sms1875/ModuCar/modeling/0217 프론트에 보여줄 이미지 추출/10. 냉동모듈.JPG

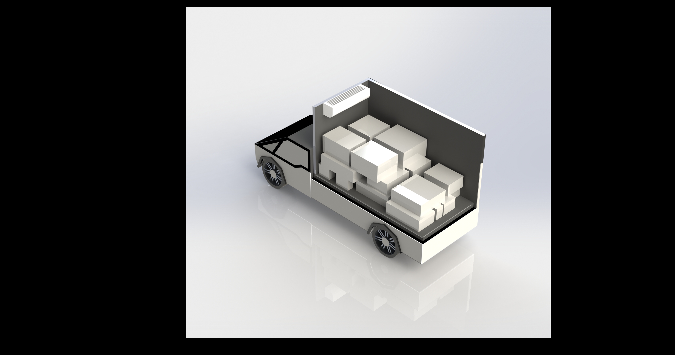
modeling/0217 프론트에 보여줄 이미지 추출/10. 냉동모듈.JPG
