sms1875/ModuCar/modeling/0217 프론트에 보여줄 이미지 추출/12. 기본 장착 상태.JPG

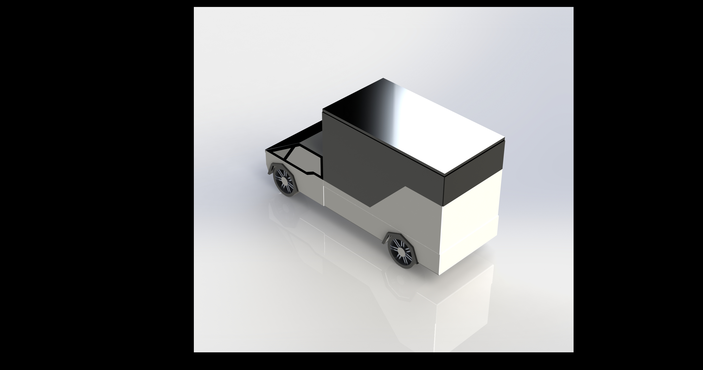
modeling/0217 프론트에 보여줄 이미지 추출/12. 기본 장착 상태.JPG
