sms1875/ModuCar/modeling/0217 프론트에 보여줄 이미지 추출/검은색 배경 지운거/0. 베이스차량.JPG

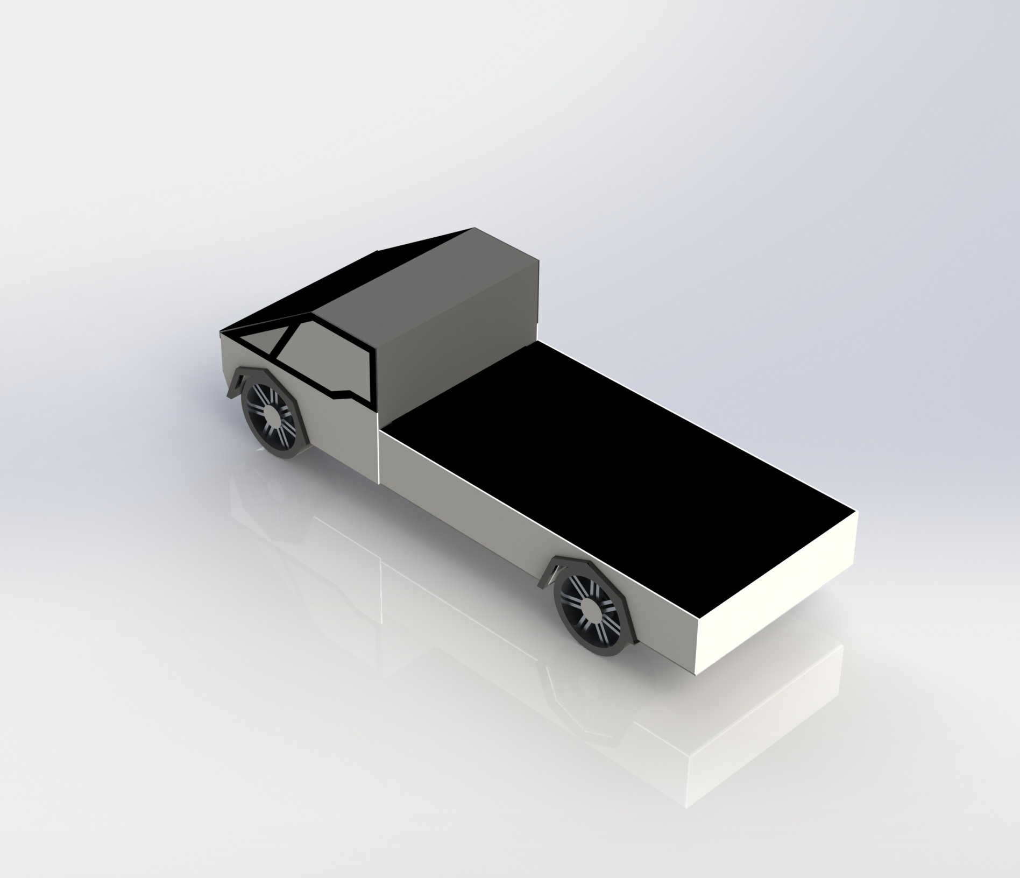
modeling/0217 프론트에 보여줄 이미지 추출/검은색 배경 지운거/0. 베이스차량.JPG
