sms1875/ModuCar/modeling/새로운 프로젝트2.gif

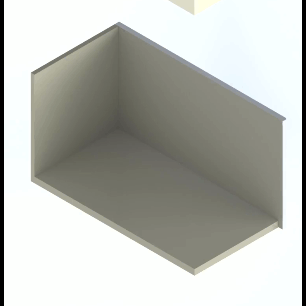
modeling/새로운 프로젝트2.gif
