sms1875/ModuCar/modeling/하늘에서 떨어지기 최종.gif

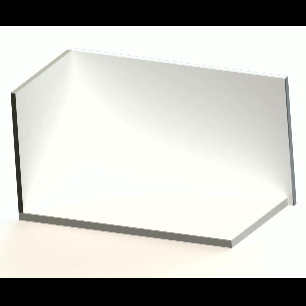
modeling/하늘에서 떨어지기 최종.gif
