sms1875/ModuCar/modeling/0215받침대/어셈블리1.SLDASM

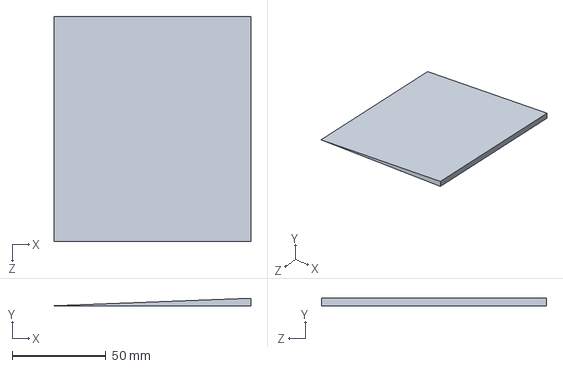
[picture p109: CAD file, 2025-02-21]
modeling/0215받침대/어셈블리1.SLDASM
105.0 x 4.00 x 120.0 mm
