sms1875/ModuCar/modeling/0202모듈/01. 깡통 모듈/깡통 모듈.SLDPRT

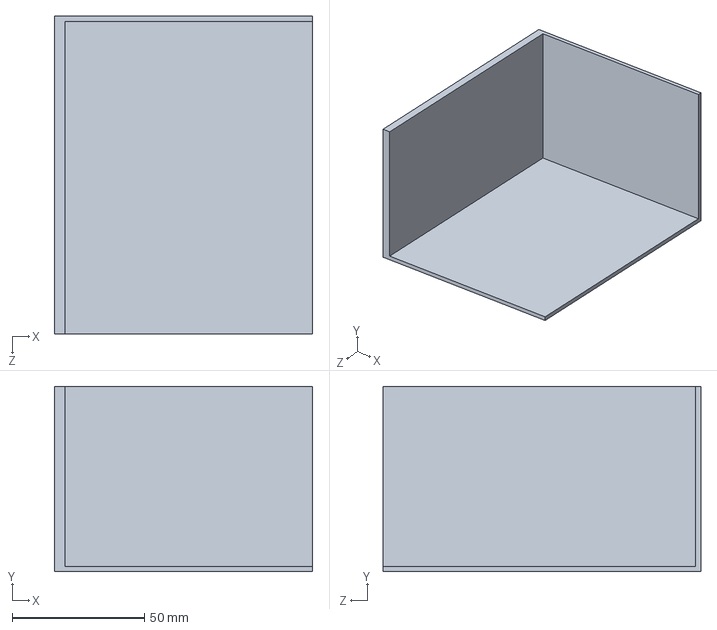
[picture p111: CAD file, 2025-02-21]
modeling/0202모듈/01. 깡통 모듈/깡통 모듈.SLDPRT
97.5 x 70.0 x 120.0 mm
