sms1875/ModuCar/modeling/0203_3D프린팅/새지지대.SLDPRT

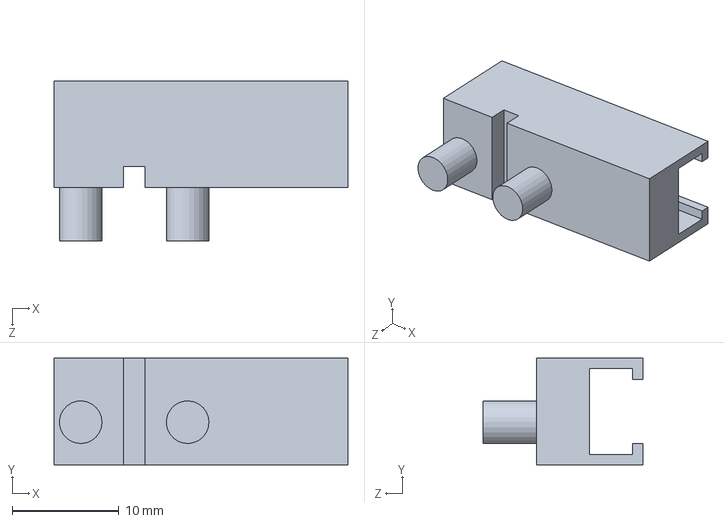
[picture p112: CAD file, 2025-02-21]
modeling/0203_3D프린팅/새지지대.SLDPRT
27.5 x 10.0 x 15.0 mm
