sms1875/ModuCar/modeling/0203오린카/부품/IMU.SLDPRT

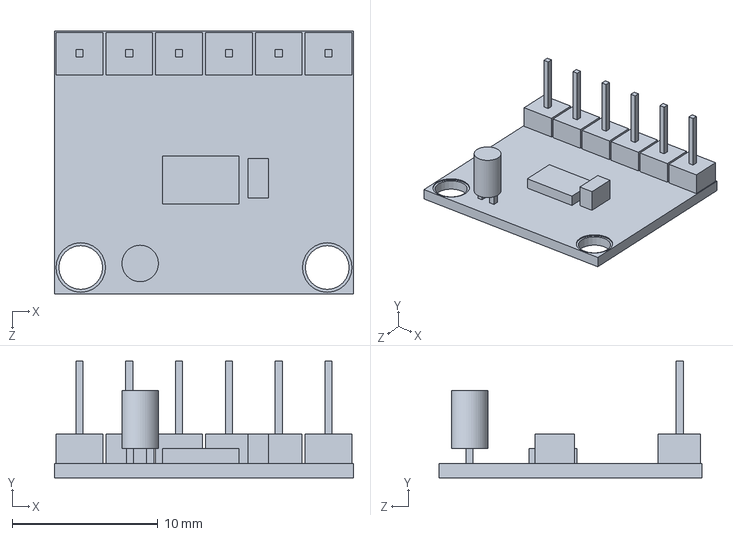
[picture p113: CAD file, 2025-02-21]
modeling/0203오린카/부품/IMU.SLDPRT
20.5 x 8.00 x 18.0 mm
