sms1875/ModuCar/modeling/0203오린카/젯슨_플레이트.SLDPRT

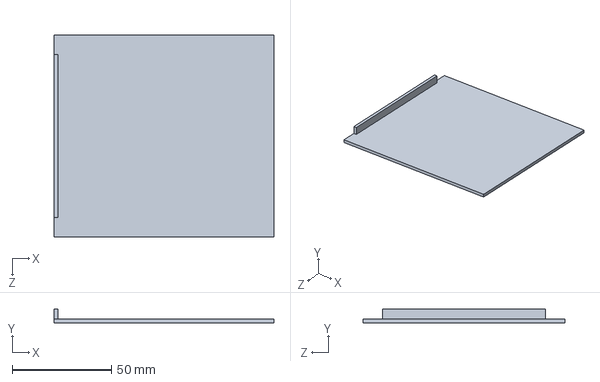
[picture p114: CAD file, 2025-02-21]
modeling/0203오린카/젯슨_플레이트.SLDPRT
110.9 x 7.00 x 102.0 mm
