sms1875/ModuCar/modeling/0206오린카/0206오린카_하단.SLDPRT

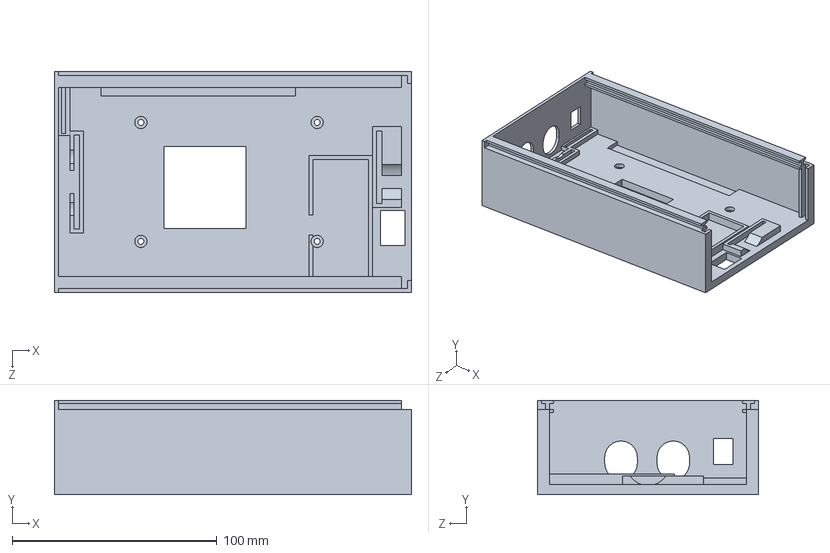
[picture p115: CAD file, 2025-02-21]
modeling/0206오린카/0206오린카_하단.SLDPRT
174.2 x 46.0 x 108.0 mm
