sms1875/ModuCar/modeling/0209오린카(프론트)/01. 배송 모듈/배송 모듈.SLDPRT

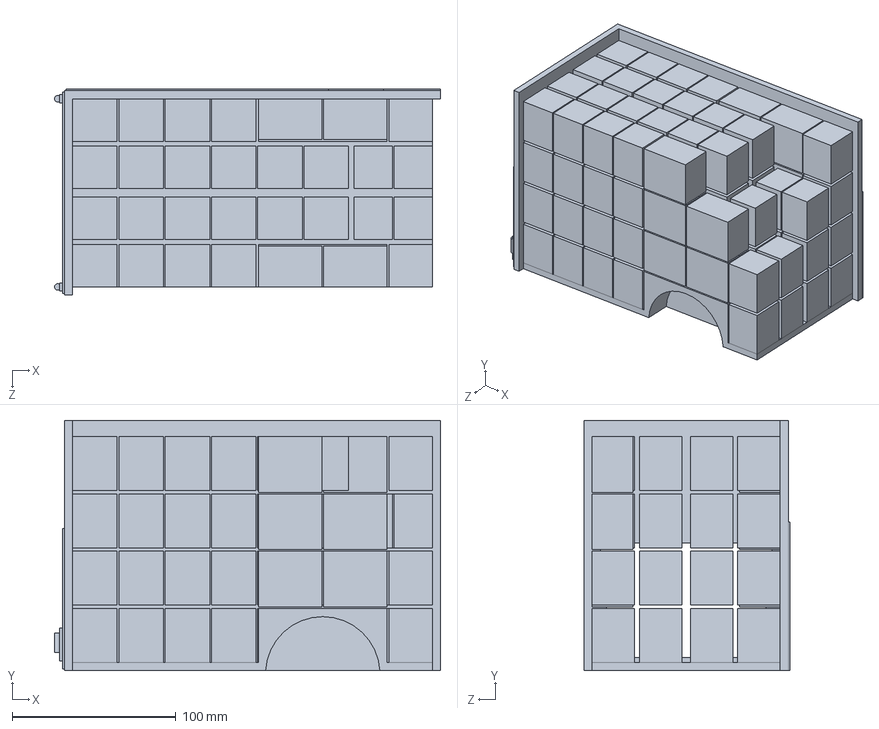
[picture p116: CAD file, 2025-02-21]
modeling/0209오린카(프론트)/01. 배송 모듈/배송 모듈.SLDPRT
236.0 x 153.0 x 126.0 mm
