sms1875/ModuCar/modeling/0209오린카(프론트)/02. 캠핑 모듈/캠핑 모듈.SLDPRT

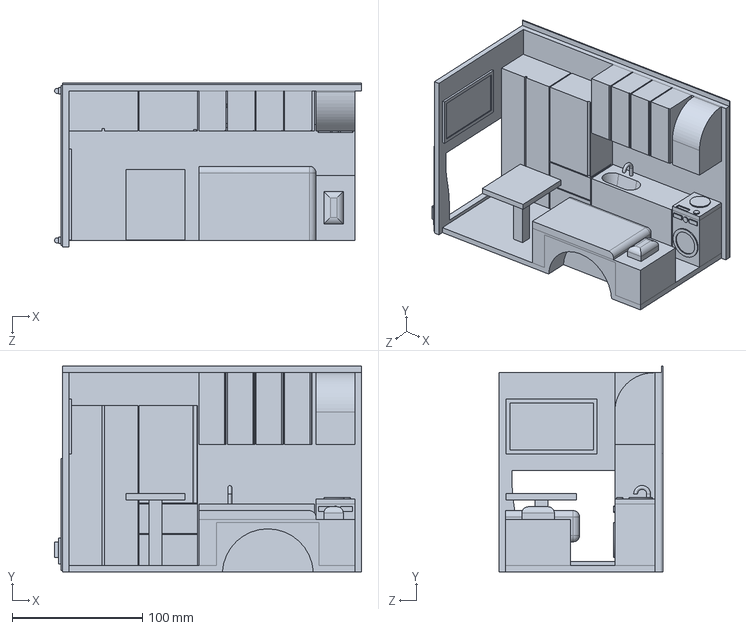
[picture p117: CAD file, 2025-02-21]
modeling/0209오린카(프론트)/02. 캠핑 모듈/캠핑 모듈.SLDPRT
236.0 x 158.0 x 126.0 mm
