sms1875/ModuCar/modeling/0209오린카(프론트)/03. 오피스 모듈/노트북1.SLDPRT

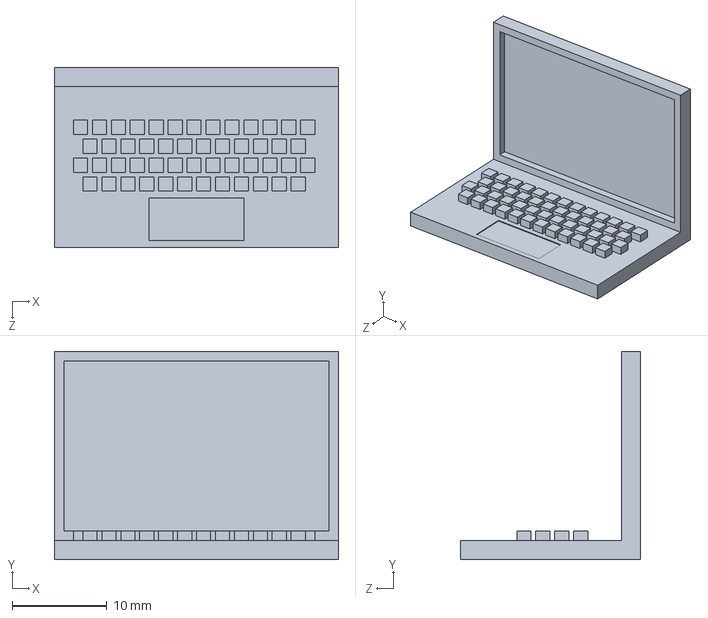
[picture p118: CAD file, 2025-02-21]
modeling/0209오린카(프론트)/03. 오피스 모듈/노트북1.SLDPRT
30.0 x 22.0 x 19.0 mm
