sms1875/ModuCar/modeling/0209오린카(프론트)/04. 화장실 모듈/변기.SLDPRT

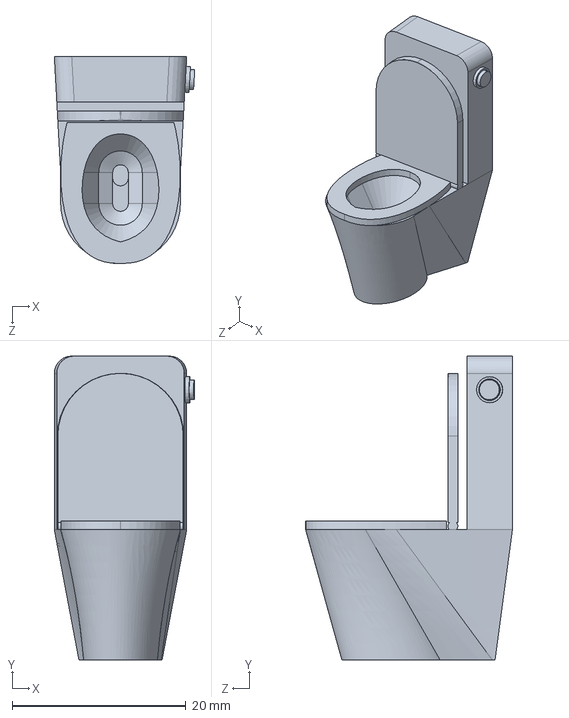
[picture p119: CAD file, 2025-02-21]
modeling/0209오린카(프론트)/04. 화장실 모듈/변기.SLDPRT
16.2 x 35.0 x 23.8 mm
