sms1875/ModuCar/modeling/0209오린카(프론트)/06. 카페 모듈/컵1.SLDPRT

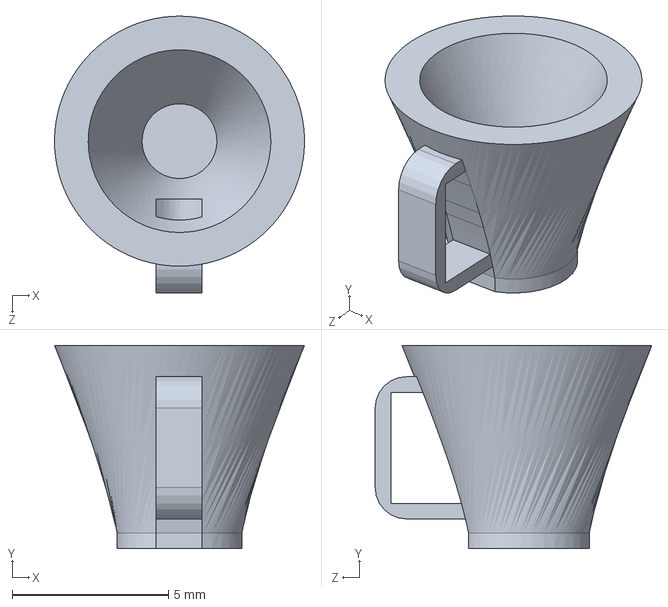
[picture p120: CAD file, 2025-02-21]
modeling/0209오린카(프론트)/06. 카페 모듈/컵1.SLDPRT
8.00 x 6.50 x 8.85 mm
