sms1875/ModuCar/modeling/0214 모듈최종/모듈/1. 베이스 모듈 (완성)/베이스모듈.SLDPRT

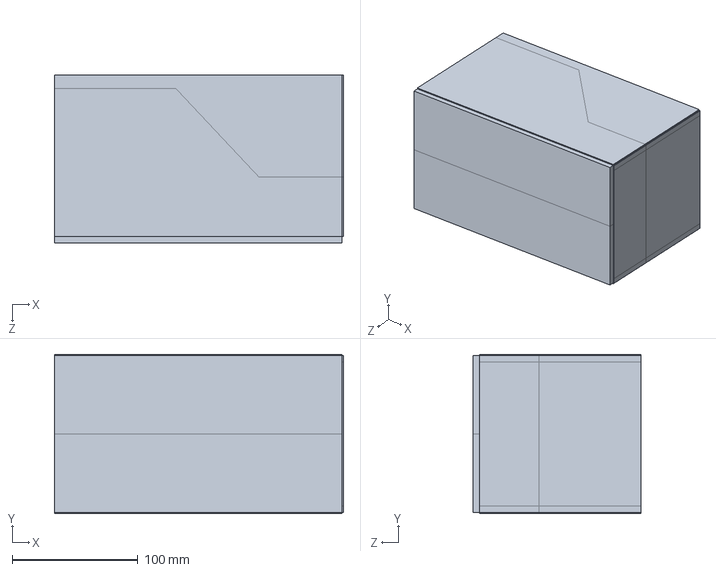
[picture p121: CAD file, 2025-02-21]
modeling/0214 모듈최종/모듈/1. 베이스 모듈 (완성)/베이스모듈.SLDPRT
230.0 x 126.9 x 133.4 mm
