sms1875/ModuCar/modeling/0214 모듈최종/모듈/10. 냉동 모듈 (완성)/냉동 모듈.SLDPRT

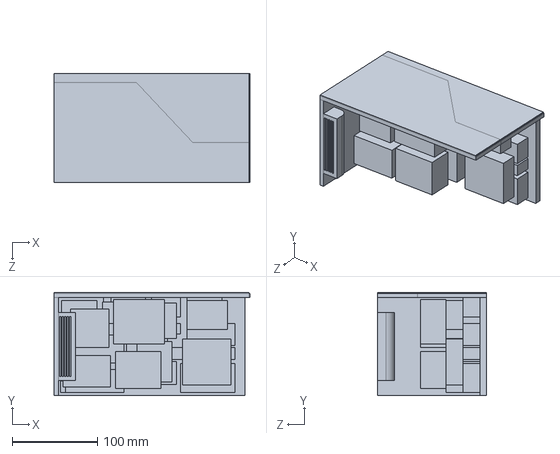
[picture p122: CAD file, 2025-02-21]
modeling/0214 모듈최종/모듈/10. 냉동 모듈 (완성)/냉동 모듈.SLDPRT
230.0 x 120.9 x 128.4 mm
