sms1875/ModuCar/modeling/0214 모듈최종/모듈/4. 화장실 모듈 (완성)/변기.SLDPRT

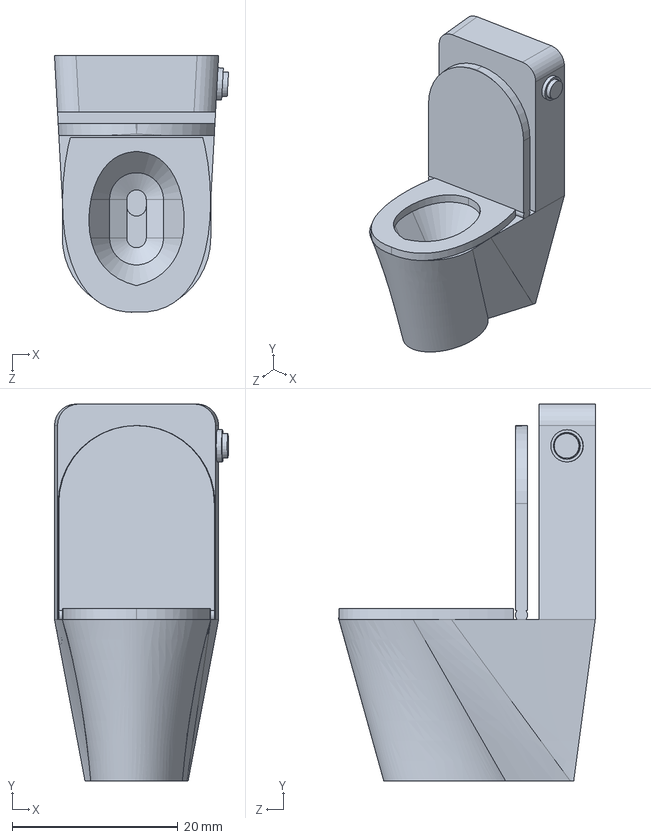
[picture p125: CAD file, 2025-02-21]
modeling/0214 모듈최종/모듈/4. 화장실 모듈 (완성)/변기.SLDPRT
21.0 x 45.5 x 31.0 mm
