sms1875/ModuCar/modeling/0215오린카뒷문/뒷문/0215오린카_뒷문1.SLDPRT

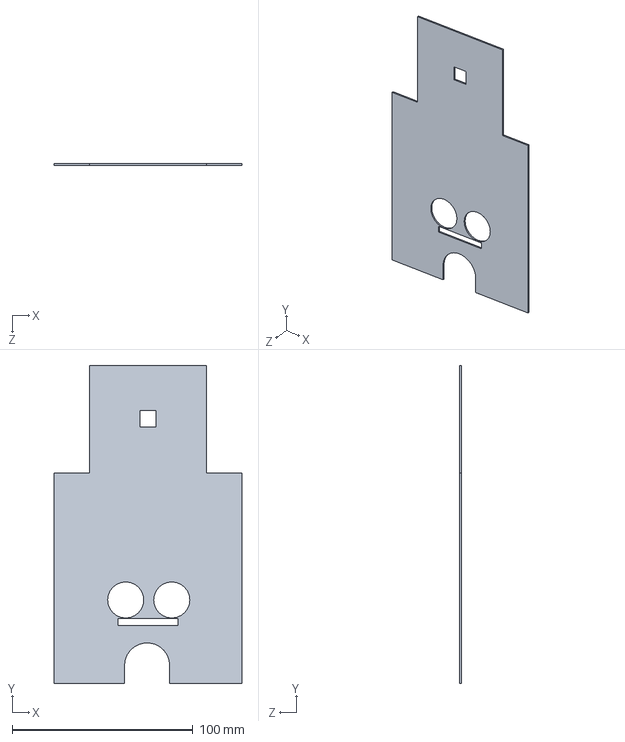
[picture p126: CAD file, 2025-02-21]
modeling/0215오린카뒷문/뒷문/0215오린카_뒷문1.SLDPRT
104.0 x 176.1 x 1.00 mm
