sms1875/ModuCar/modeling/0220조립시뮬레이션/뒷문/카메라4mm벽1.SLDPRT

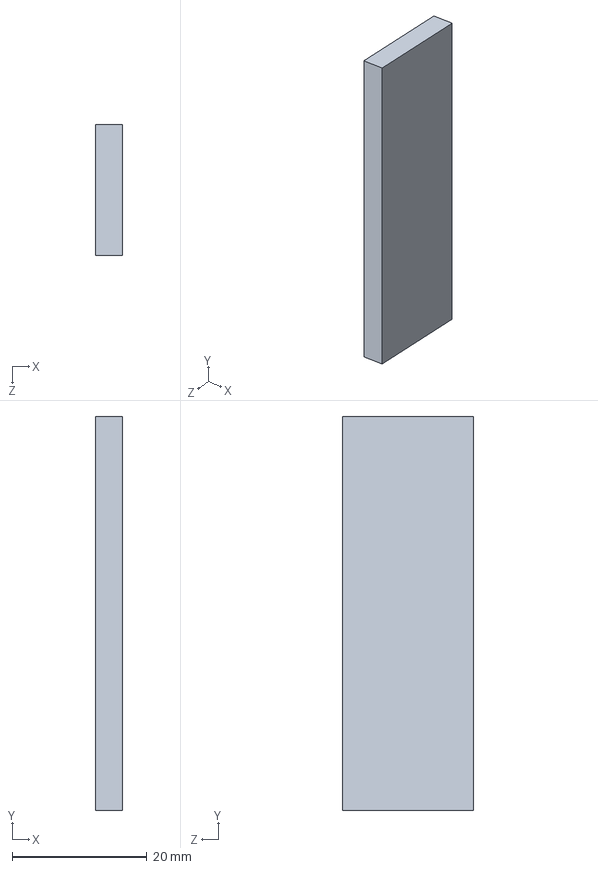
[picture p127: CAD file, 2025-02-21]
modeling/0220조립시뮬레이션/뒷문/카메라4mm벽1.SLDPRT
4.00 x 58.5 x 19.5 mm
