sms1875/ModuCar/modeling/0220조립시뮬레이션/오린카상단/0208오린카_뒷문1.SLDPRT

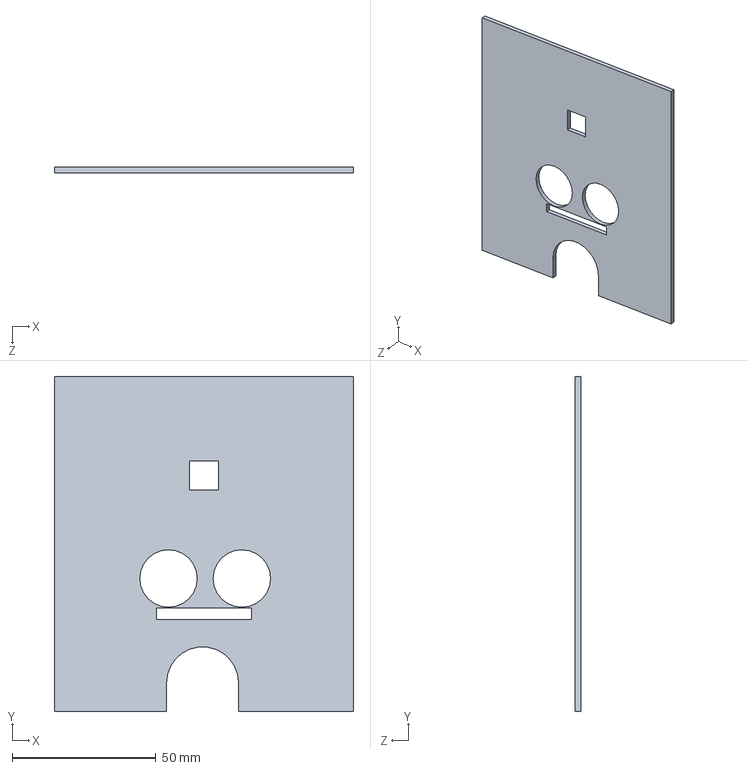
[picture p128: CAD file, 2025-02-21]
modeling/0220조립시뮬레이션/오린카상단/0208오린카_뒷문1.SLDPRT
104.0 x 116.5 x 2.00 mm
