sms1875/ModuCar/modeling/1안.SLDPRT

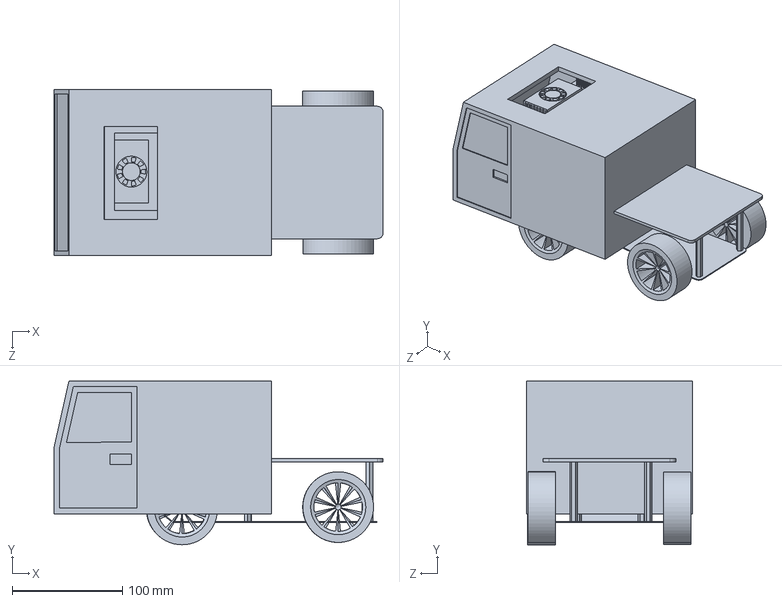
[picture p129: CAD file, 2025-02-21]
modeling/1안.SLDPRT
297.9 x 148.1 x 150.3 mm
