sms1875/ModuCar/modeling/3d프린팅할것/STL/오린카케이스_뒷문_결합.STL

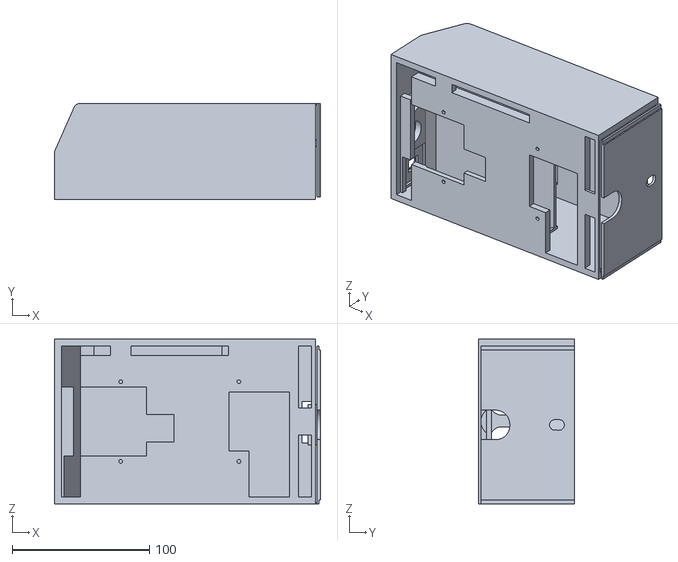
[picture p130: CAD file, 2025-02-21]
modeling/3d프린팅할것/STL/오린카케이스_뒷문_결합.STL
193.5 x 70.0 x 120.0
