sms1875/ModuCar/modeling/리프트/arm.SLDPRT

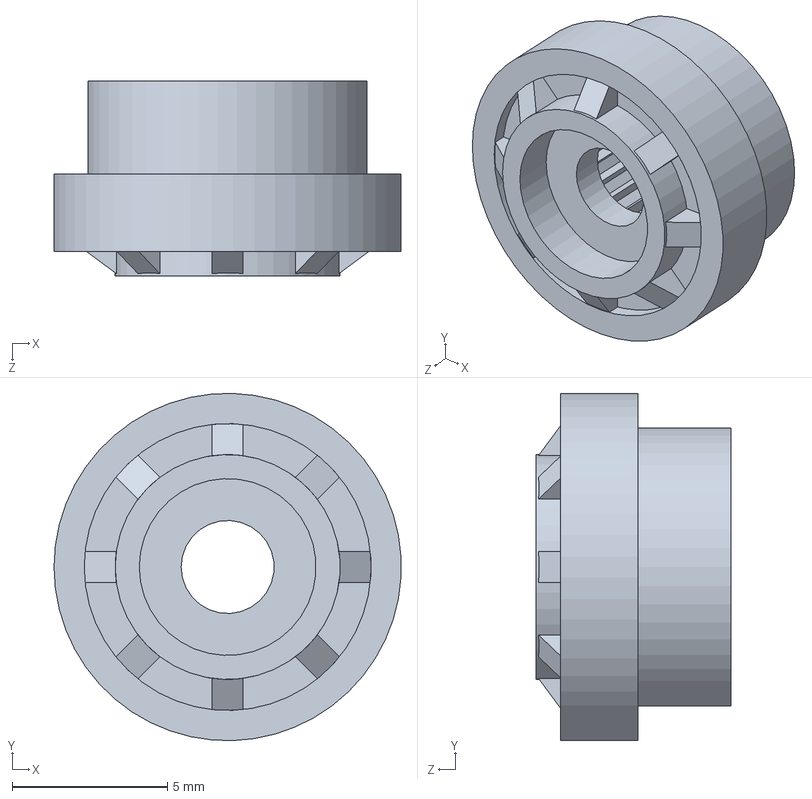
[picture p131: CAD file, 2025-02-21]
modeling/리프트/arm.SLDPRT
11.2 x 11.2 x 6.30 mm
