sms1875/ModuCar/modeling/오린카/정밀아크릴_배터리_젯슨_파트.SLDPRT

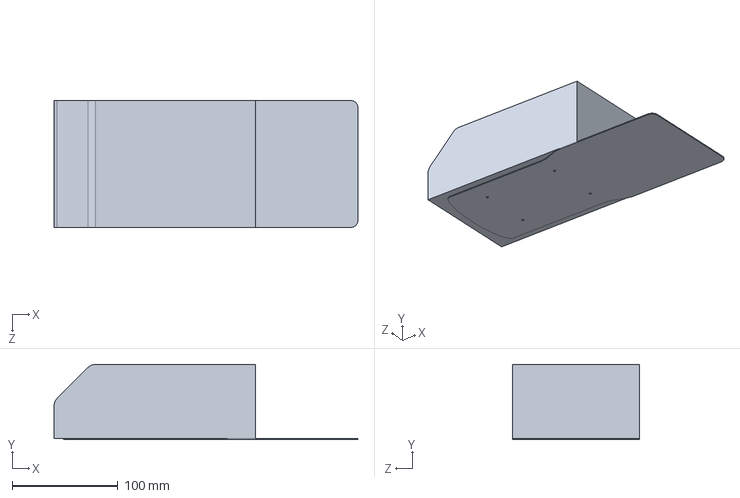
[picture p132: CAD file, 2025-02-21]
modeling/오린카/정밀아크릴_배터리_젯슨_파트.SLDPRT
287.0 x 71.0 x 120.0 mm
