sms1875/ModuCar/modeling/0203오린카/부품/정밀 아크릴판.SLDPRT

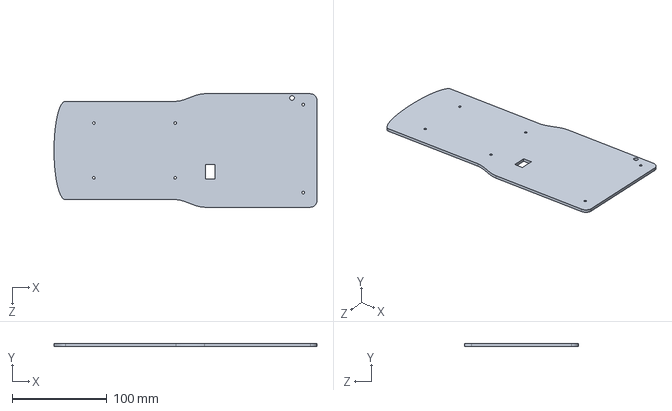
[picture p133: CAD file, 2025-02-21]
modeling/0203오린카/부품/정밀 아크릴판.SLDPRT
278.0 x 3.00 x 120.0 mm
