sms1875/ModuCar/modeling/0206_3D프린팅/코어_회전작대기.SLDPRT

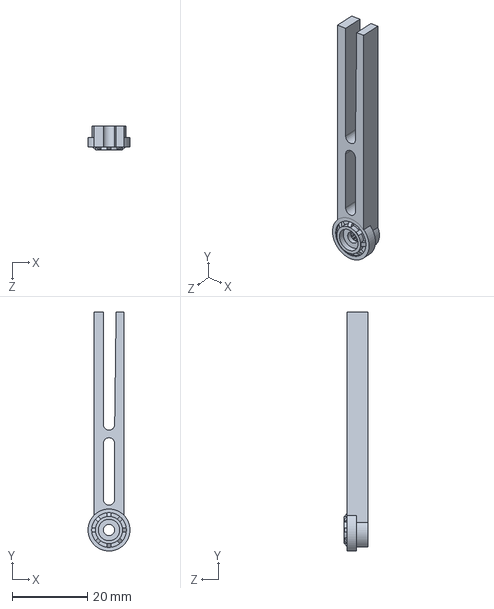
[picture p134: CAD file, 2025-02-21]
modeling/0206_3D프린팅/코어_회전작대기.SLDPRT
11.2 x 63.7 x 6.30 mm
