sms1875/ModuCar/modeling/0206오린카/뒷문_상단.SLDPRT

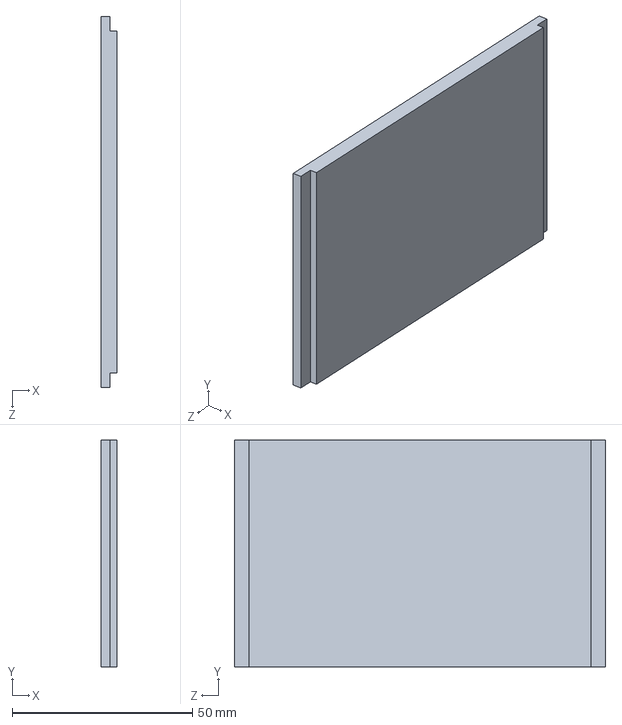
[picture p135: CAD file, 2025-02-21]
modeling/0206오린카/뒷문_상단.SLDPRT
4.50 x 63.0 x 103.0 mm
