sms1875/ModuCar/modeling/0209오린카(프론트)/04. 화장실 모듈/남자변기.SLDPRT

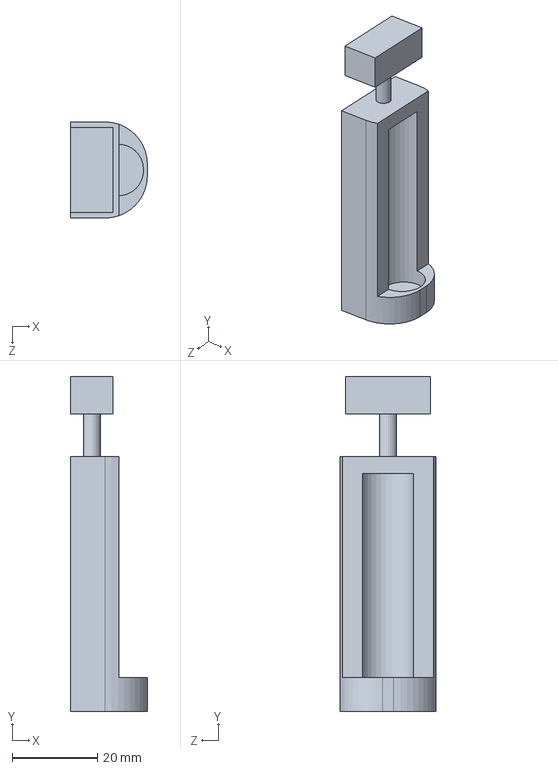
[picture p136: CAD file, 2025-02-21]
modeling/0209오린카(프론트)/04. 화장실 모듈/남자변기.SLDPRT
18.1 x 78.8 x 22.6 mm
