sms1875/ModuCar/modeling/0209오린카(프론트)/베이스차량.SLDPRT

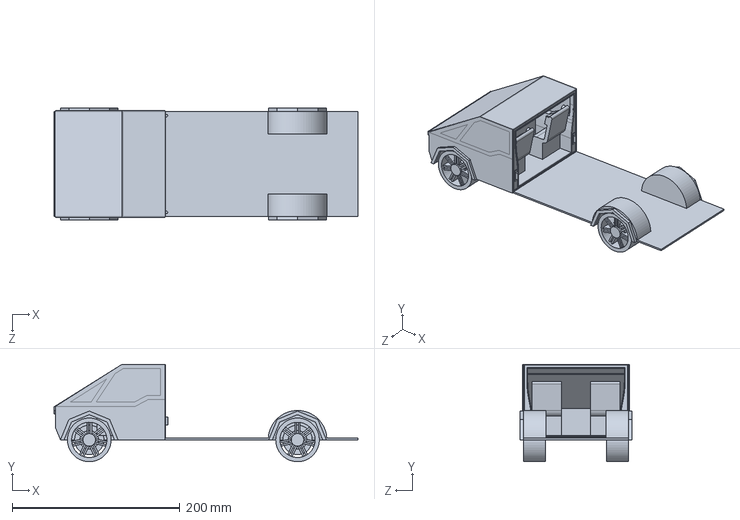
[picture p137: CAD file, 2025-02-21]
modeling/0209오린카(프론트)/베이스차량.SLDPRT
362.0 x 116.0 x 133.0 mm
