sms1875/ModuCar/modeling/0214 모듈최종/모듈/3. 캠핑 모듈 (완성)/캠핑 모듈.SLDPRT

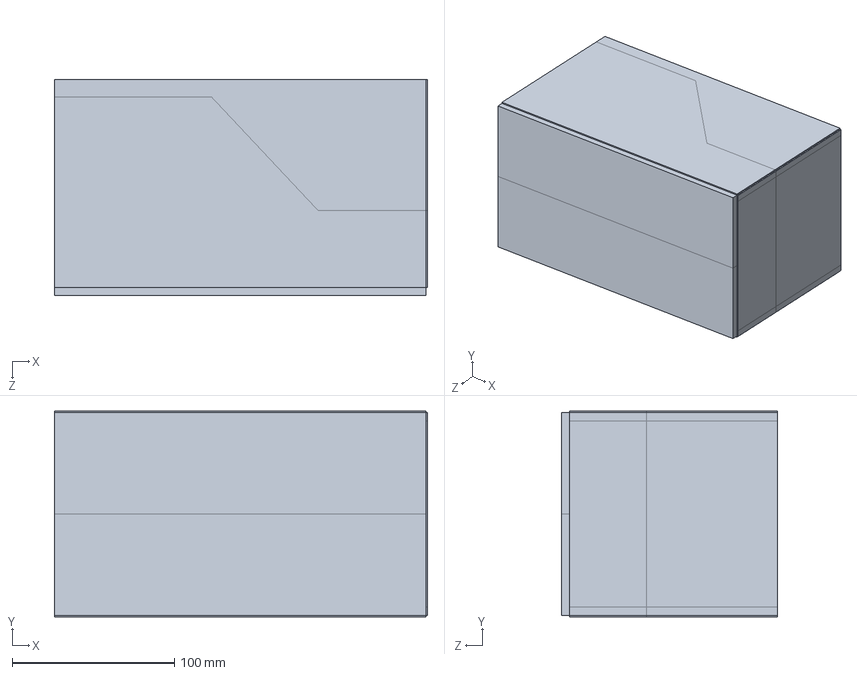
[picture p138: CAD file, 2025-02-21]
modeling/0214 모듈최종/모듈/3. 캠핑 모듈 (완성)/캠핑 모듈.SLDPRT
230.0 x 126.9 x 133.4 mm
