sms1875/ModuCar/modeling/0215오린카뒷문/카메라1mm문.SLDPRT

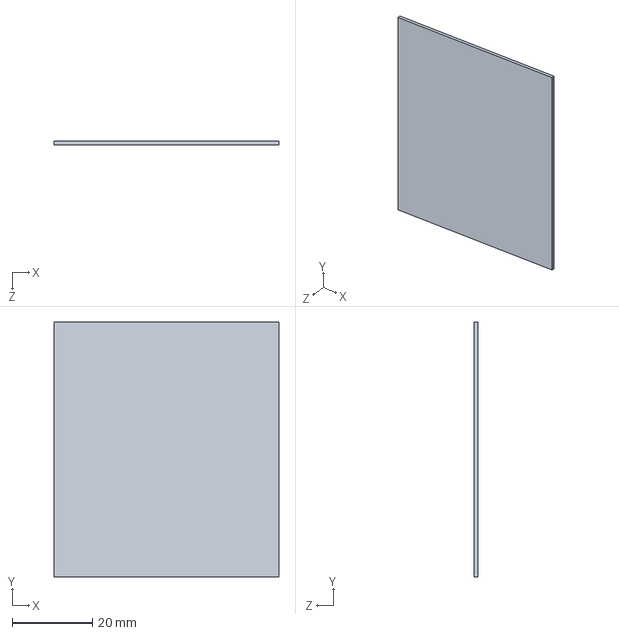
[picture p139: CAD file, 2025-02-21]
modeling/0215오린카뒷문/카메라1mm문.SLDPRT
56.0 x 63.5 x 1.00 mm
