sms1875/ModuCar/modeling/0220조립시뮬레이션/오린카상단/초음파센서받침대.SLDPRT

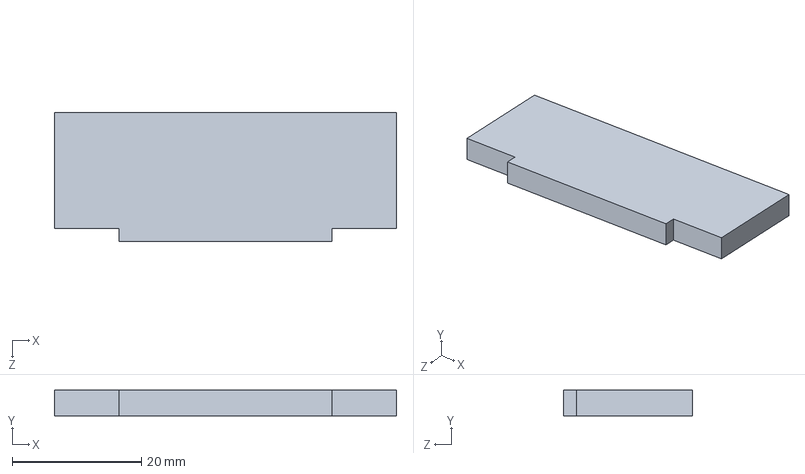
[picture p140: CAD file, 2025-02-21]
modeling/0220조립시뮬레이션/오린카상단/초음파센서받침대.SLDPRT
53.0 x 4.00 x 20.0 mm
