sms1875/ModuCar/modeling/3d프린팅할것/화장실_캠핑_결합.SLDPRT

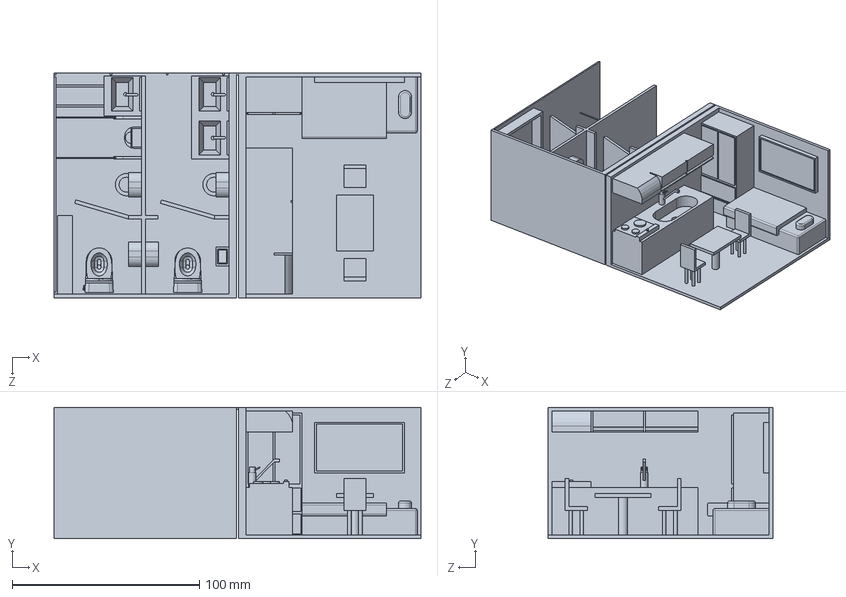
[picture p141: CAD file, 2025-02-21]
modeling/3d프린팅할것/화장실_캠핑_결합.SLDPRT
196.0 x 70.0 x 120.0 mm
