sms1875/ModuCar/modeling/오린카/정밀 아크릴판.SLDPRT

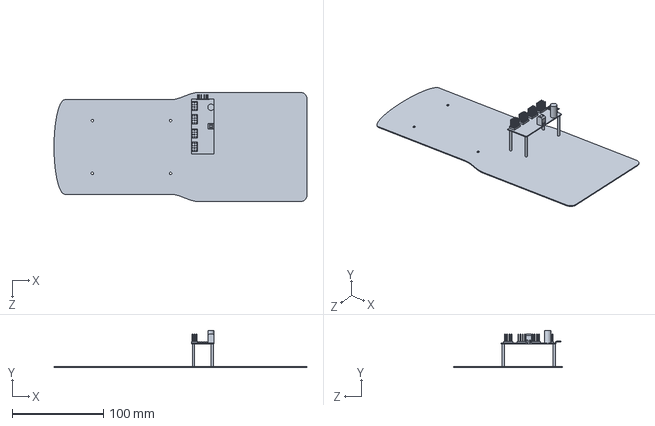
[picture p142: CAD file, 2025-02-21]
modeling/오린카/정밀 아크릴판.SLDPRT
278.0 x 41.0 x 120.0 mm
