sms1875/ModuCar/modeling/0203오린카/0203오린카_상단.SLDPRT

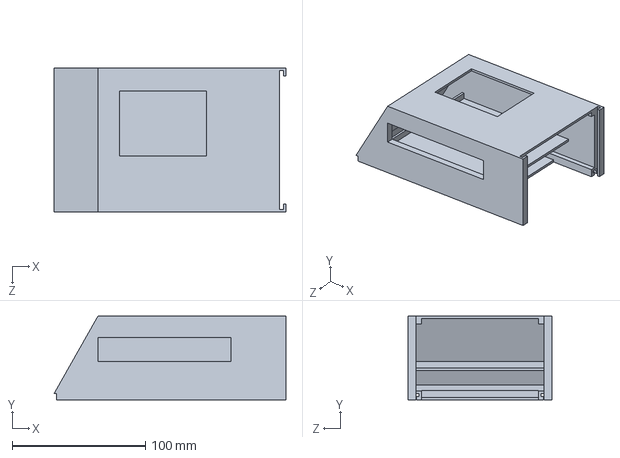
[picture p143: CAD file, 2025-02-21]
modeling/0203오린카/0203오린카_상단.SLDPRT
174.2 x 63.0 x 108.0 mm
