sms1875/ModuCar/modeling/0203오린카/부품/배터리.SLDPRT

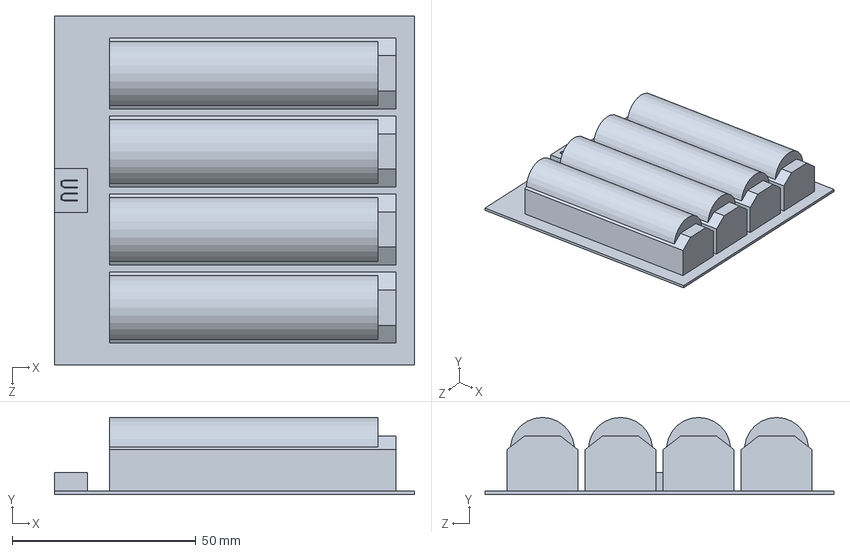
[picture p144: CAD file, 2025-02-21]
modeling/0203오린카/부품/배터리.SLDPRT
98.0 x 21.0 x 95.0 mm
