sms1875/ModuCar/modeling/0206오린카/뒷문_하단.SLDPRT

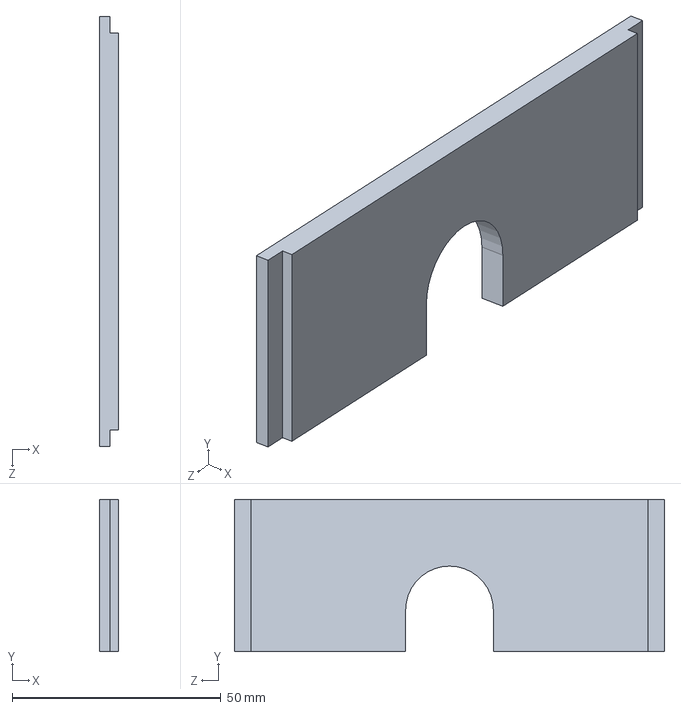
[picture p145: CAD file, 2025-02-21]
modeling/0206오린카/뒷문_하단.SLDPRT
4.50 x 36.5 x 103.0 mm
