sms1875/ModuCar/modeling/0208오린카/0208오린카_뒷문.SLDPRT

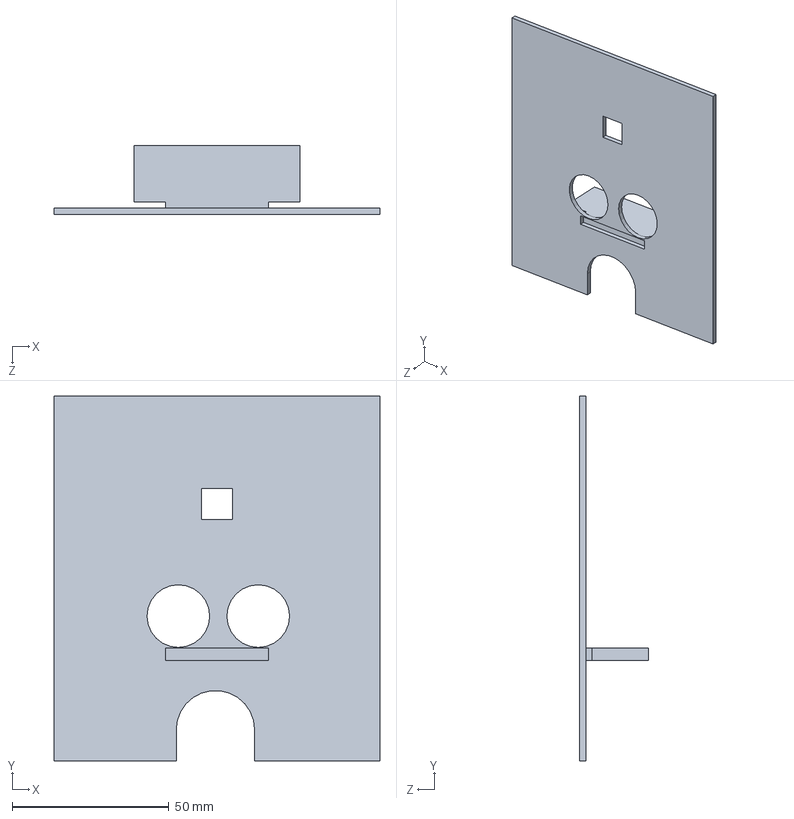
[picture p146: CAD file, 2025-02-21]
modeling/0208오린카/0208오린카_뒷문.SLDPRT
104.0 x 116.5 x 22.0 mm
