sms1875/ModuCar/modeling/0209오린카(프론트)/04. 화장실 모듈/화장실 모듈.SLDPRT

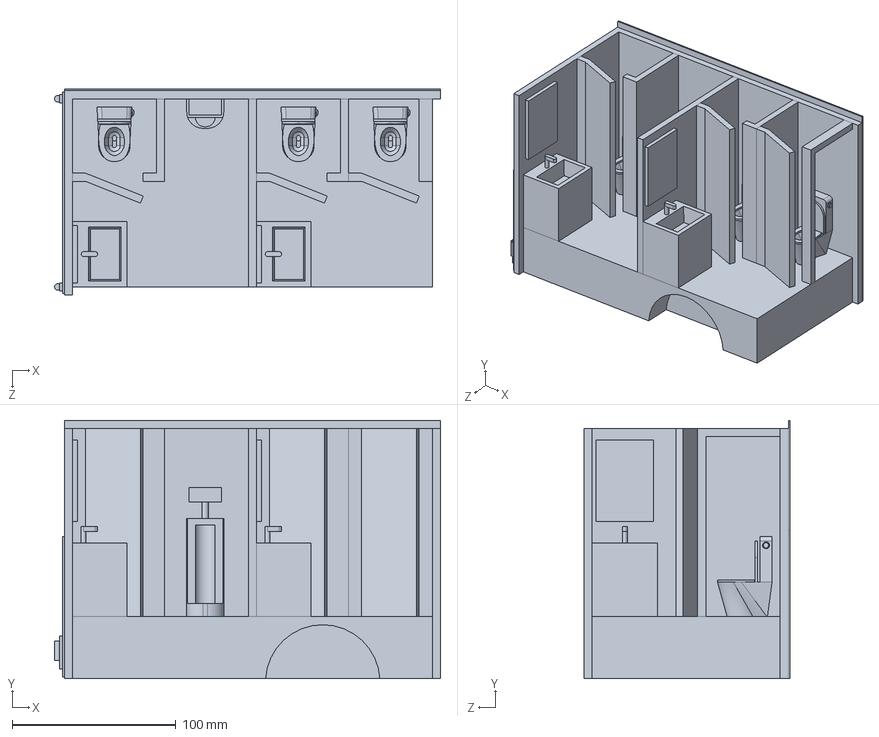
[picture p147: CAD file, 2025-02-21]
modeling/0209오린카(프론트)/04. 화장실 모듈/화장실 모듈.SLDPRT
236.0 x 158.0 x 126.0 mm
