sms1875/ModuCar/modeling/0209오린카(프론트)/베이스모듈.SLDPRT

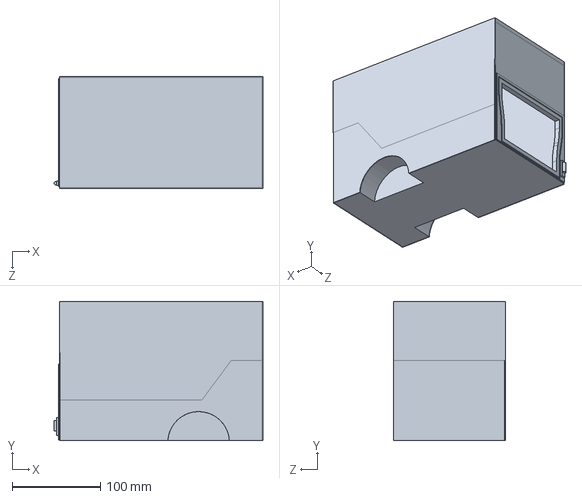
[picture p148: CAD file, 2025-02-21]
modeling/0209오린카(프론트)/베이스모듈.SLDPRT
237.0 x 158.0 x 127.0 mm
