sms1875/ModuCar/modeling/0214 모듈최종/모듈/4. 화장실 모듈 (완성)/화장실 모듈.SLDPRT

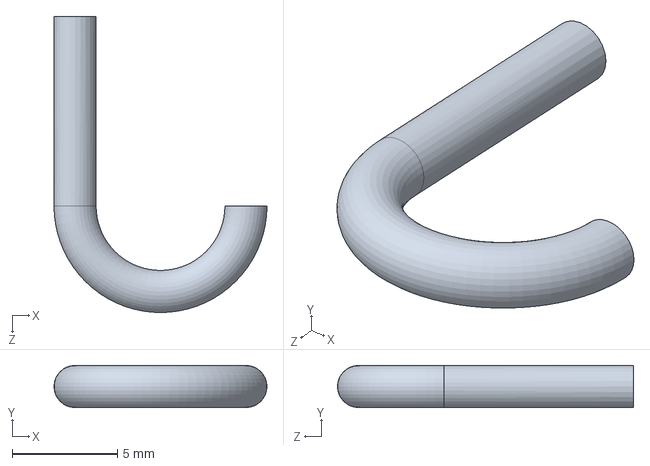
[picture p149: CAD file, 2025-02-21]
modeling/0214 모듈최종/모듈/4. 화장실 모듈 (완성)/화장실 모듈.SLDPRT
10.1 x 2.00 x 14.1 mm
