sms1875/ModuCar/modeling/0215받침대/모듈.SLDPRT

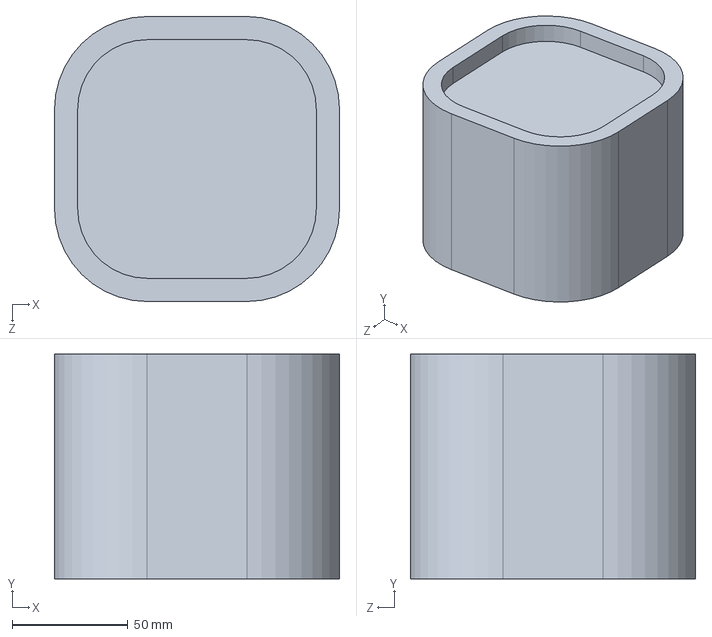
[picture p150: CAD file, 2025-02-21]
modeling/0215받침대/모듈.SLDPRT
123.0 x 97.0 x 123.0 mm
