sms1875/ModuCar/modeling/0215오린카뒷문/카메라4mm 바깥레일1.SLDPRT

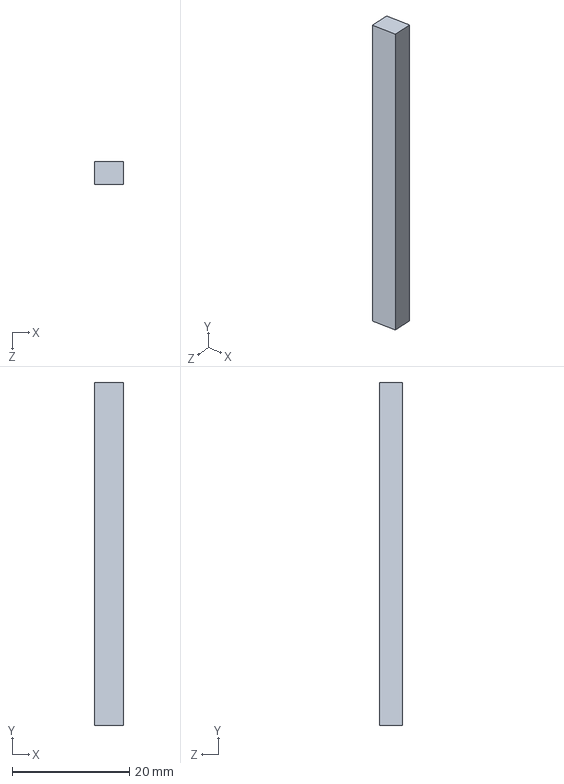
[picture p152: CAD file, 2025-02-21]
modeling/0215오린카뒷문/카메라4mm 바깥레일1.SLDPRT
5.00 x 58.5 x 4.00 mm
