sms1875/ModuCar/modeling/0220조립시뮬레이션/배터리.SLDPRT

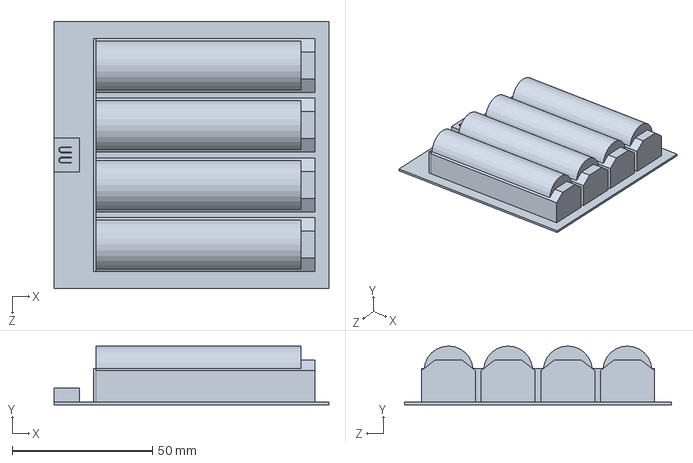
[picture p153: CAD file, 2025-02-21]
modeling/0220조립시뮬레이션/배터리.SLDPRT
98.0 x 21.0 x 95.0 mm
