sms1875/ModuCar/modeling/8_8_12_큐브.SLDPRT

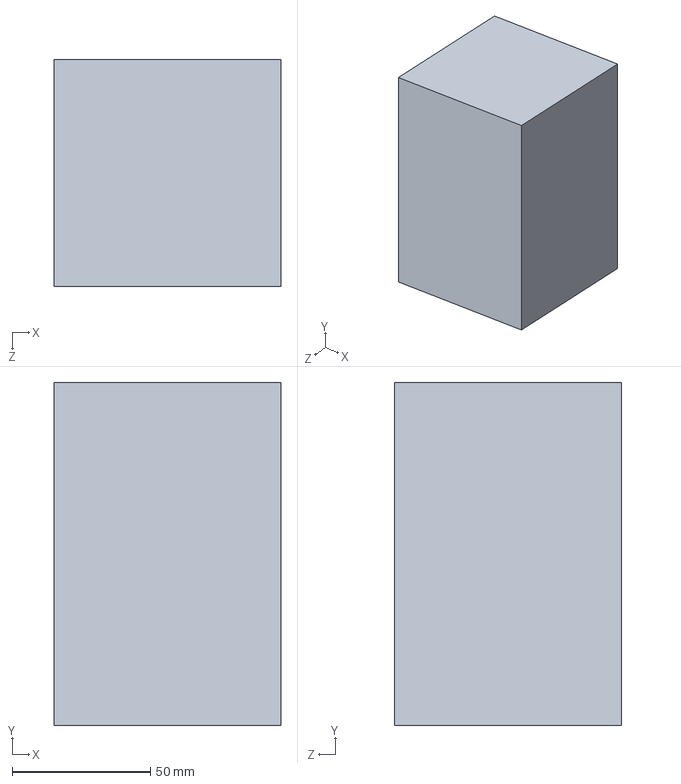
[picture p154: CAD file, 2025-02-21]
modeling/8_8_12_큐브.SLDPRT
82.0 x 124.0 x 82.0 mm
