sms1875/ModuCar/modeling/리프트/원형돌출 슬라이드.SLDPRT

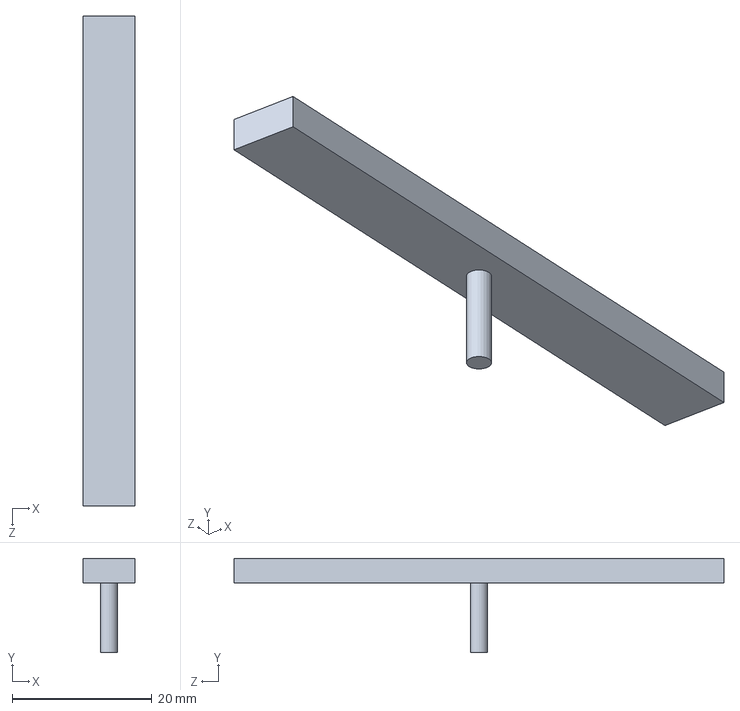
[picture p155: CAD file, 2025-02-21]
modeling/리프트/원형돌출 슬라이드.SLDPRT
7.50 x 13.5 x 70.0 mm
