sms1875/ModuCar/modeling/0203_3D프린팅/오린카상단_뒷문상단_뒷문하단_리프트에달판자_새지지대_원형돌출슬라이드_코어회전작대기_파트.SLDPRT

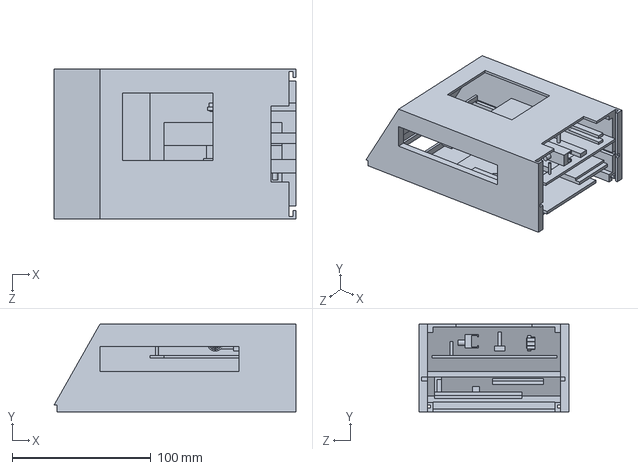
[picture p156: CAD file, 2025-02-21]
modeling/0203_3D프린팅/오린카상단_뒷문상단_뒷문하단_리프트에달판자_새지지대_원형돌출슬라이드_코어회전작대기_파트.SLDPRT
174.2 x 63.0 x 108.0 mm
