sms1875/ModuCar/modeling/0203오린카/부품/전자석.SLDPRT

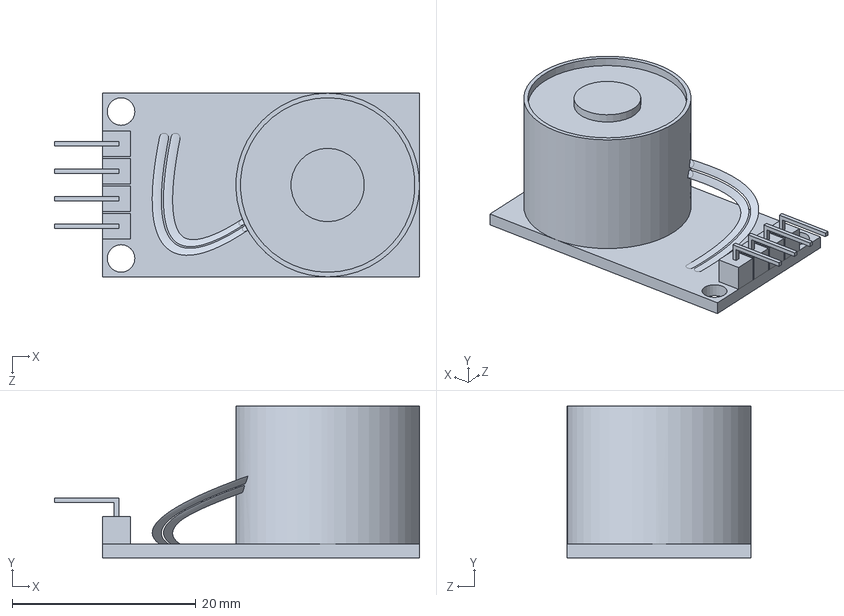
[picture p157: CAD file, 2025-02-21]
modeling/0203오린카/부품/전자석.SLDPRT
39.8 x 16.5 x 20.0 mm
