sms1875/ModuCar/modeling/0214 모듈최종/베이스차량.SLDPRT

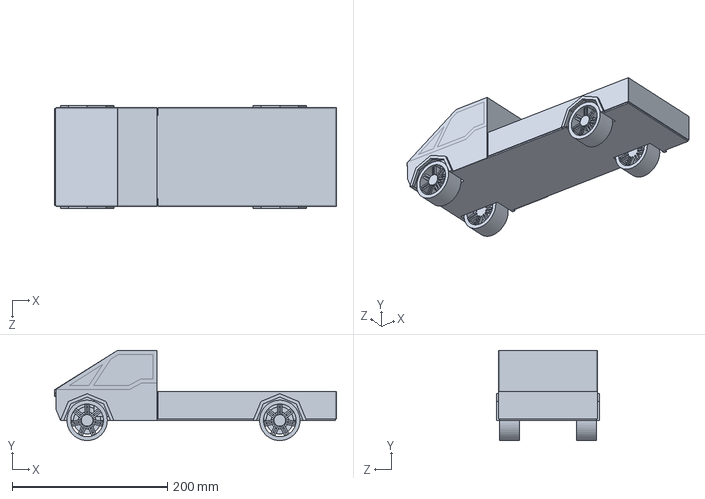
[picture p158: CAD file, 2025-02-21]
modeling/0214 모듈최종/베이스차량.SLDPRT
363.0 x 116.0 x 133.0 mm
