sms1875/ModuCar/modeling/0215오린카뒷문/파트5.SLDPRT

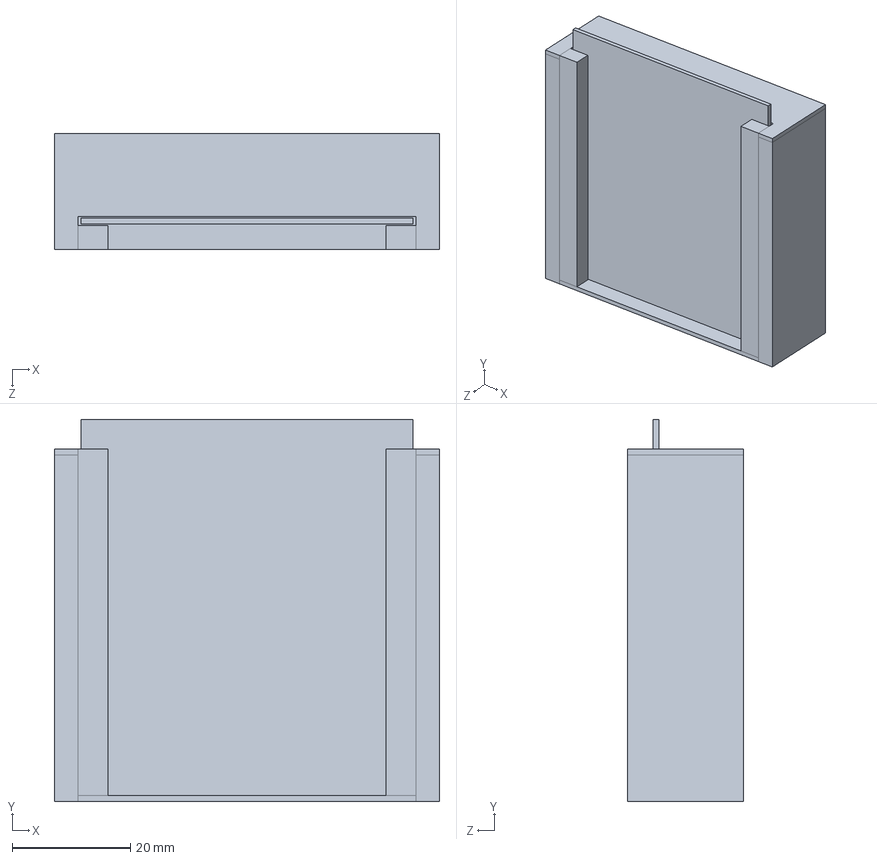
[picture p159: CAD file, 2025-02-21]
modeling/0215오린카뒷문/파트5.SLDPRT
65.0 x 64.5 x 19.5 mm
