sms1875/ModuCar/modeling/0220조립시뮬레이션/오린카상단/0208오린카_상단.SLDPRT

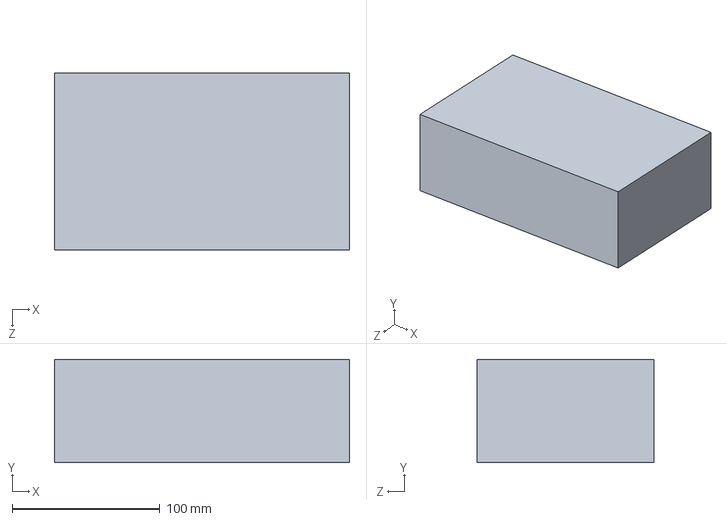
[picture p160: CAD file, 2025-02-21]
modeling/0220조립시뮬레이션/오린카상단/0208오린카_상단.SLDPRT
200.0 x 70.0 x 120.0 mm
