sms1875/ModuCar/modeling/0220조립시뮬레이션/csi카메라.SLDPRT

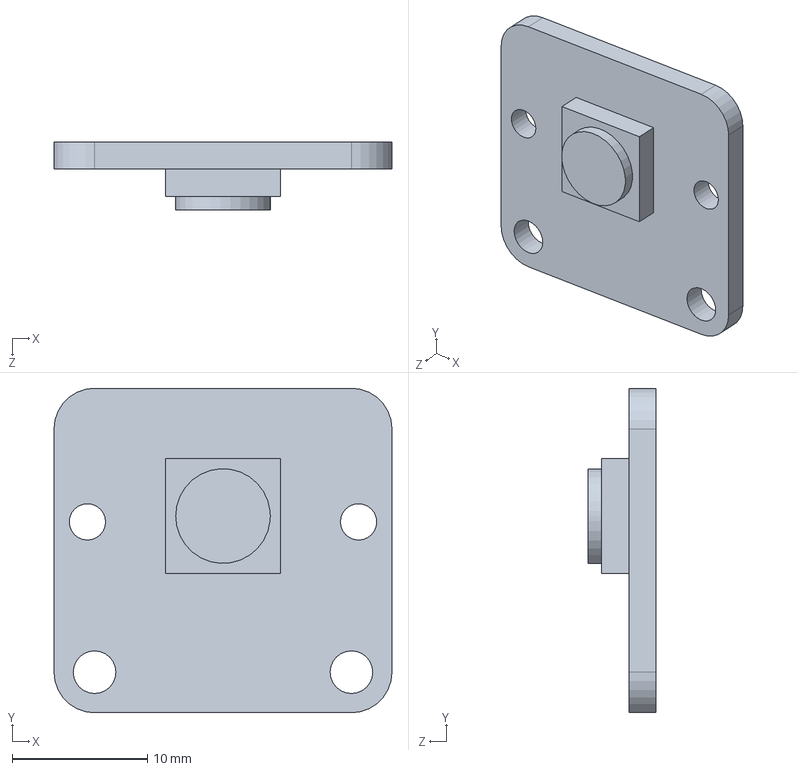
[picture p161: CAD file, 2025-02-21]
modeling/0220조립시뮬레이션/csi카메라.SLDPRT
25.0 x 24.0 x 5.00 mm
