sms1875/ModuCar/modeling/0220조립시뮬레이션/오린카상단/0208오린카_상단_벽면2.SLDPRT

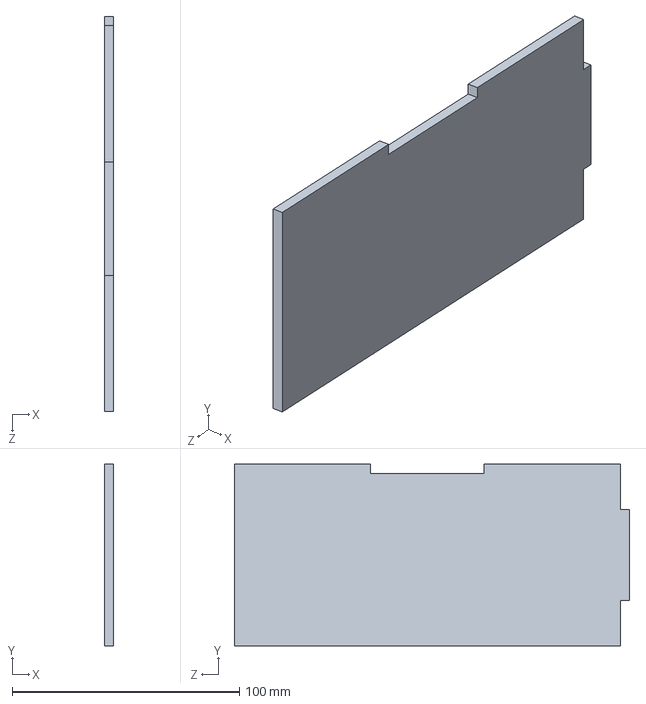
[picture p162: CAD file, 2025-02-21]
modeling/0220조립시뮬레이션/오린카상단/0208오린카_상단_벽면2.SLDPRT
4.00 x 80.0 x 174.0 mm
