sms1875/ModuCar/modeling/8_8_6큐브.SLDPRT

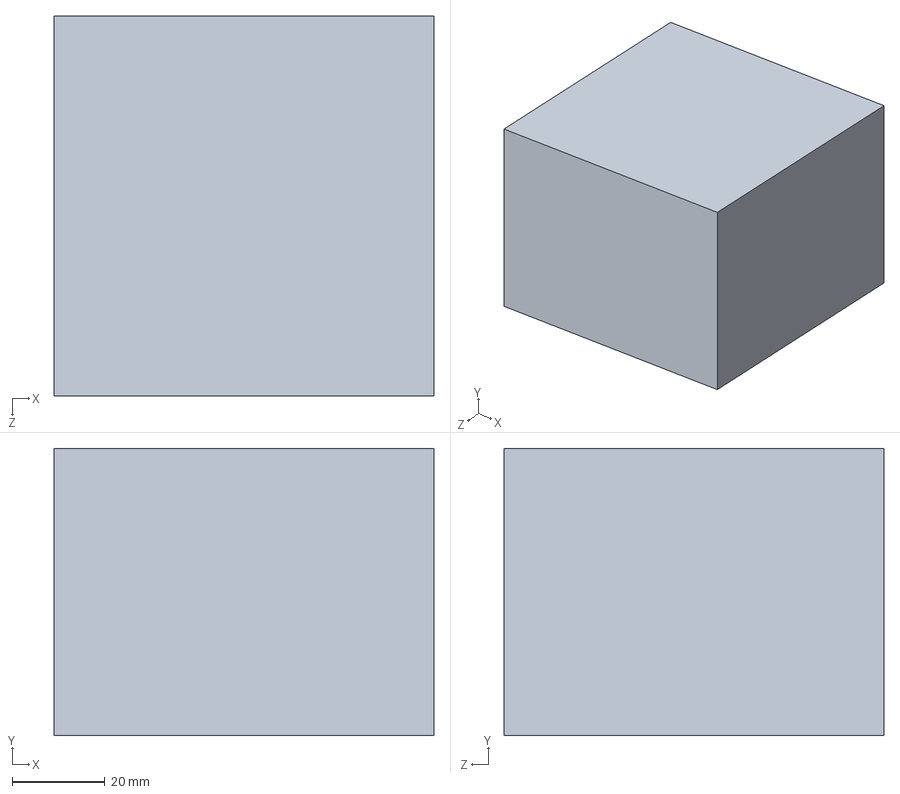
[picture p163: CAD file, 2025-02-21]
modeling/8_8_6큐브.SLDPRT
82.0 x 62.0 x 82.0 mm
