sms1875/ModuCar/modeling/0203_3D프린팅/리프트에 달 판자.SLDPRT

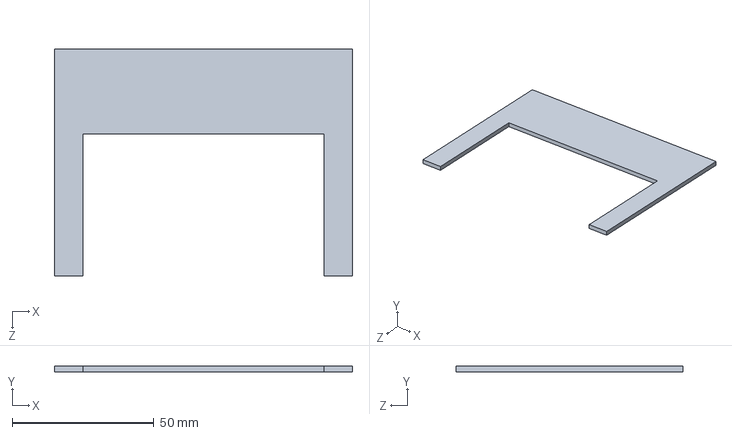
[picture p164: CAD file, 2025-02-21]
modeling/0203_3D프린팅/리프트에 달 판자.SLDPRT
105.0 x 2.00 x 80.0 mm
