sms1875/ModuCar/modeling/0206_3D프린팅/리프트에 달 판자.SLDPRT

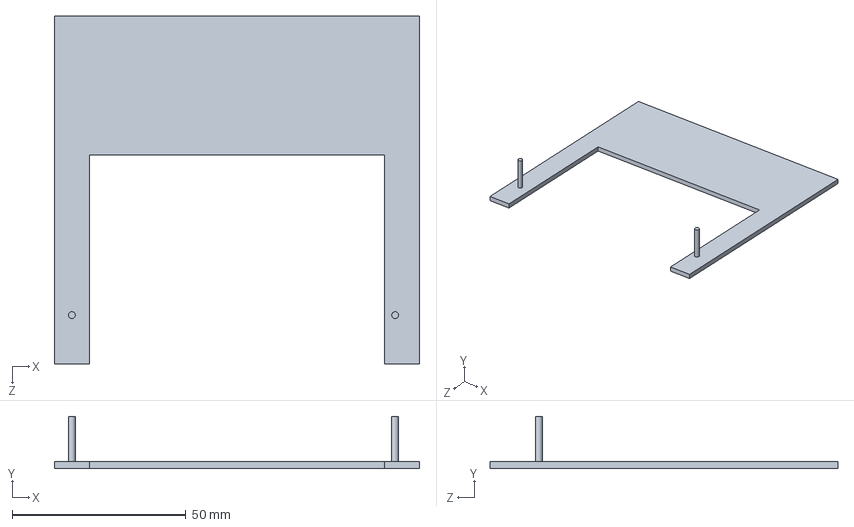
[picture p165: CAD file, 2025-02-21]
modeling/0206_3D프린팅/리프트에 달 판자.SLDPRT
105.0 x 15.0 x 100.0 mm
