sms1875/ModuCar/modeling/리프트/어셈블리2.SLDASM

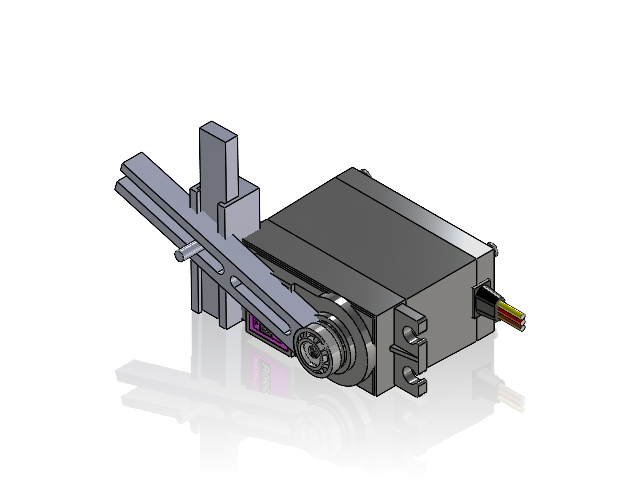
[picture p178: CAD file, 2025-02-21]
modeling/리프트/어셈블리2.SLDASM
mg996R
새지지대
원형돌출 슬라이드
코어_회전작대기
