sms1875/ModuCar/modeling/거치대 영화관 모듈 - 복사본.SLDASM

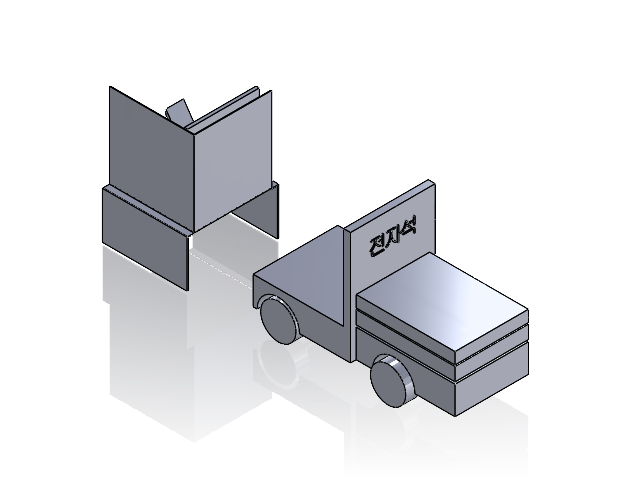
[picture p180: CAD file, 2025-02-21]
modeling/거치대 영화관 모듈 - 복사본.SLDASM
기본
모듈 거치대
영화관 모듈
