sms1875/ModuCar/modeling/오린카/책상까지 조립.SLDASM

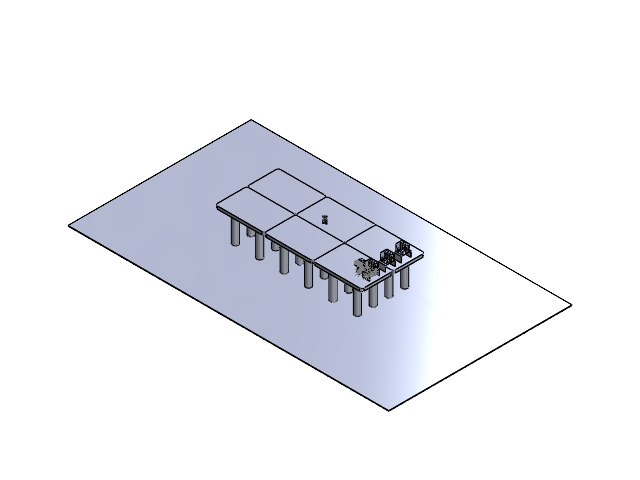
[picture p181: CAD file, 2025-02-21]
modeling/오린카/책상까지 조립.SLDASM
책상
빨래방모듈 x 3
고객
