sms1875/ModuCar/modeling/리프트/어셈블리1.SLDASM

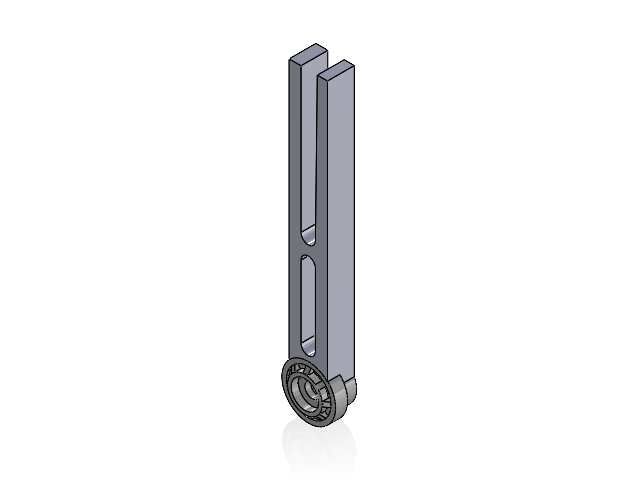
[picture p182: CAD file, 2025-02-21]
modeling/리프트/어셈블리1.SLDASM
arm
bar
