sms1875/ModuCar/modeling/0202모듈/02. 캠핑 모듈/캠핑 모듈 어셈블리.SLDASM

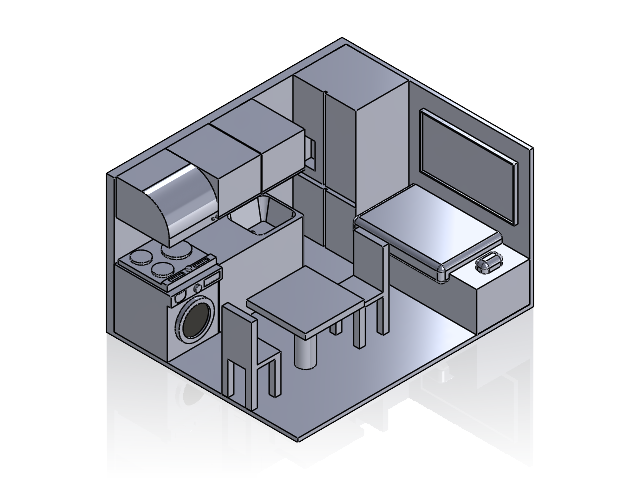
[picture p183: CAD file, 2025-02-21]
modeling/0202모듈/02. 캠핑 모듈/캠핑 모듈 어셈블리.SLDASM
바디19
바디20
바디21
바디22
바디23
바디24
바디25
바디26
바디27
바디28
바디29
바디30
바디31
바디32
바디33
바디34
바디35
