sms1875/ModuCar/modeling/0214 모듈최종/모든 모듈 어셈블리.SLDASM

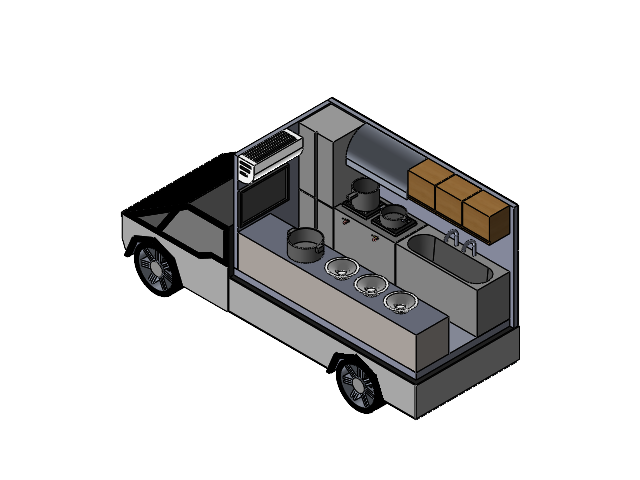
[picture p184: CAD file, 2025-02-21]
modeling/0214 모듈최종/모든 모듈 어셈블리.SLDASM
베이스차량
푸드트럭모듈
