sms1875/ModuCar/modeling/리프트/판자제작어셈블리.SLDASM

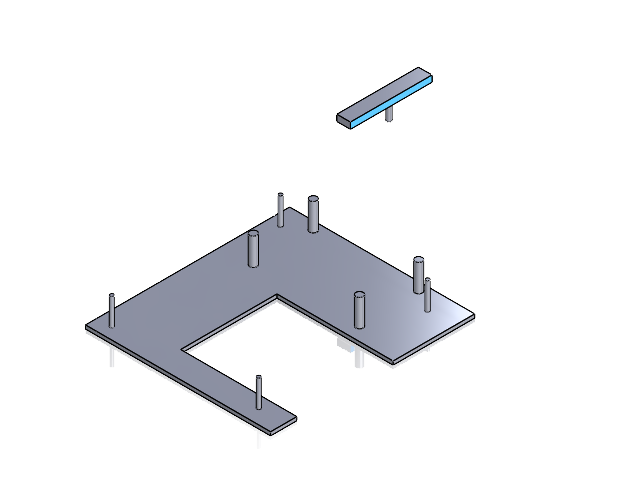
[picture p185: CAD file, 2025-02-21]
modeling/리프트/판자제작어셈블리.SLDASM
리프트에 달 판자
원형돌출 슬라이드
