sms1875/ModuCar/modeling/영화관 모듈 결합.SLDASM

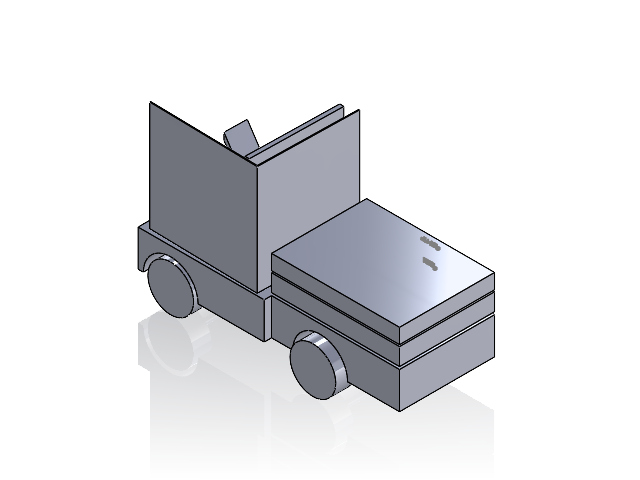
[picture p186: CAD file, 2025-02-21]
modeling/영화관 모듈 결합.SLDASM
기본
영화관 모듈
