sms1875/ModuCar/modeling/0203_3D프린팅/오린카상단_뒷문상단_뒷문하단_리프트에달판자_새지지대_원형돌출슬라이드_코어회전작대기.SLDASM

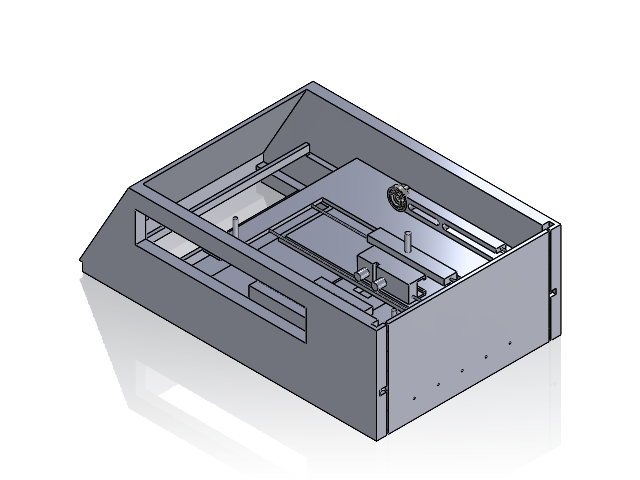
[picture p187: CAD file, 2025-02-21]
modeling/0203_3D프린팅/오린카상단_뒷문상단_뒷문하단_리프트에달판자_새지지대_원형돌출슬라이드_코어회전작대기.SLDASM
0203오린카_상단
뒷문_상단
리프트에 달 판자
새지지대
원형돌출 슬라이드
코어_회전작대기
뒷문_하단
파트1^오린카상단_뒷문상단_뒷문하단_리프트에달판자_새지지대_원형돌출슬라이드_코어회전작대기
