sms1875/ModuCar/modeling/0214 모듈최종/모듈분해된상태의어셈블리.SLDASM

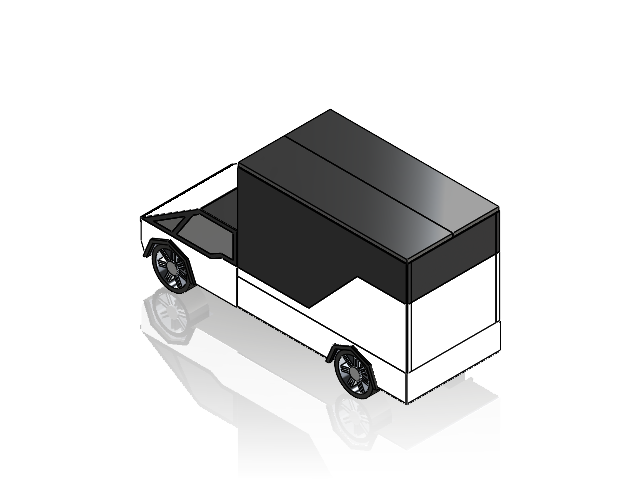
[picture p188: CAD file, 2025-02-21]
modeling/0214 모듈최종/모듈분해된상태의어셈블리.SLDASM
바닥
상단인테리어1
상단인테리어2
우측면
정면
좌측면
천장1
천장2
하단인테리어1
하단인테리어2
후면
후면상단작음1
후면상단작음2
후면상단큼1
후면하단작음1
후면하단작음2
후면하단큼1
베이스차량
