sms1875/ModuCar/modeling/0214 모듈최종/어셈블리1.SLDASM

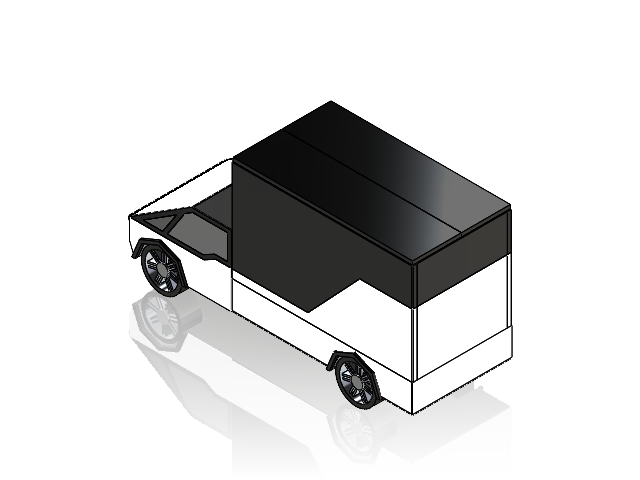
[picture p189: CAD file, 2025-02-21]
modeling/0214 모듈최종/어셈블리1.SLDASM
베이스차량
베이스모듈
